Teille98/HVGene-OpenHardware/docs/Figures/Article_Figures/Fig12_XIAO_USB_Connection.jpeg

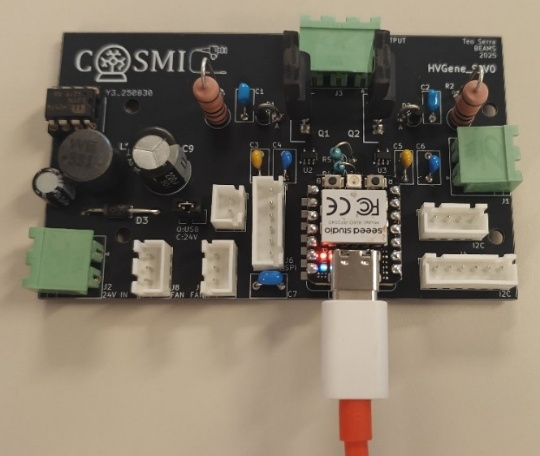
docs/Figures/Article_Figures/Fig12_XIAO_USB_Connection.jpeg
