Teille98/HVGene-OpenHardware/docs/Figures/Article_Figures/Fig_Val1_OpenCircuit.png

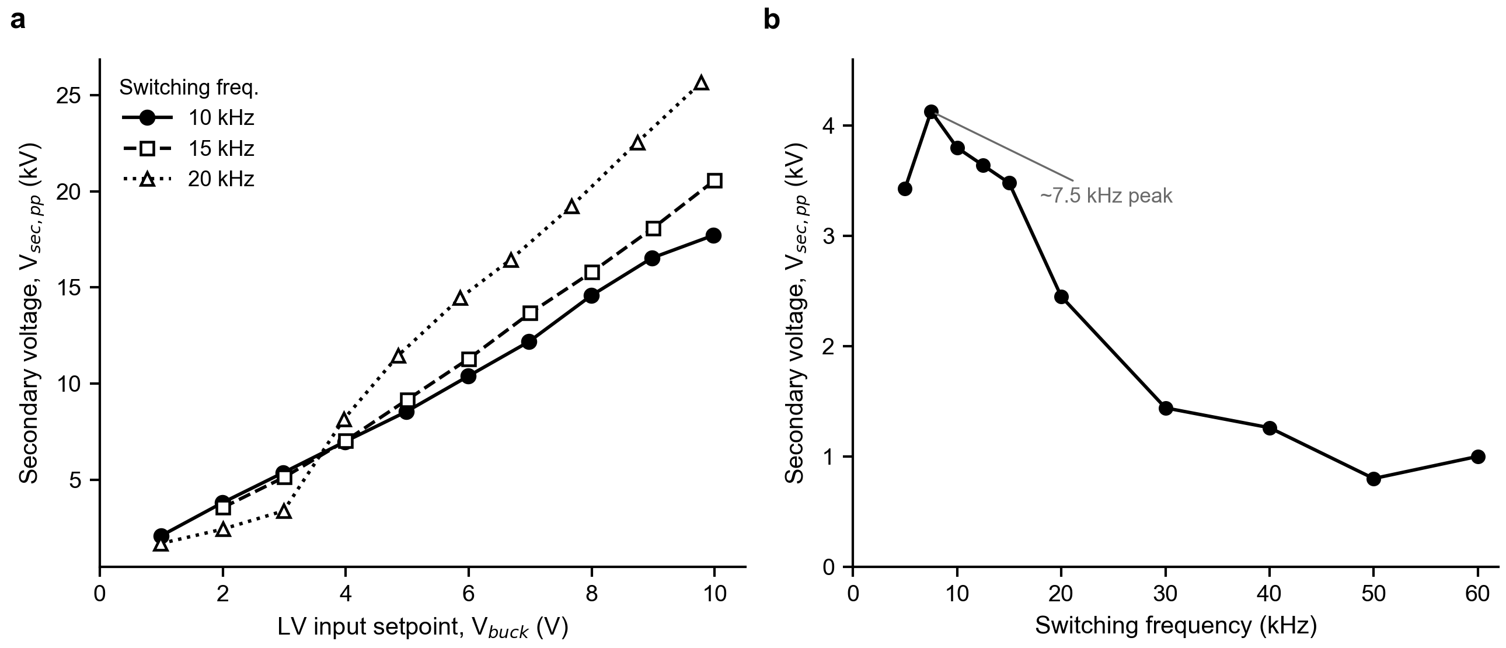
docs/Figures/Article_Figures/Fig_Val1_OpenCircuit.png
