Teille98/HVGene-OpenHardware/docs/Figures/Article_Figures/Fig_Val2_IgnitionWindow.png

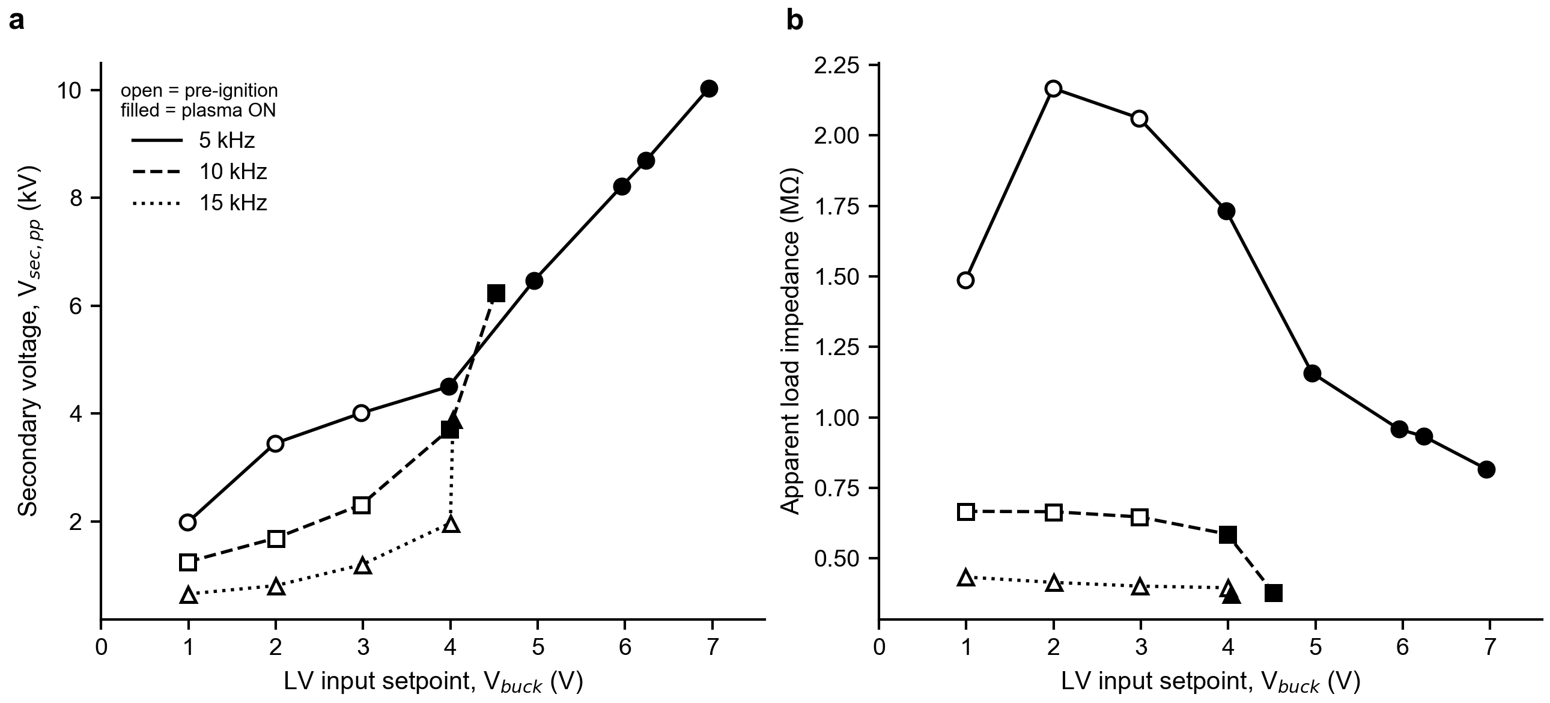
docs/Figures/Article_Figures/Fig_Val2_IgnitionWindow.png
