Teille98/HVGene-OpenHardware/docs/Figures/Article_Figures/Fig_Val3_FreqResponse.png

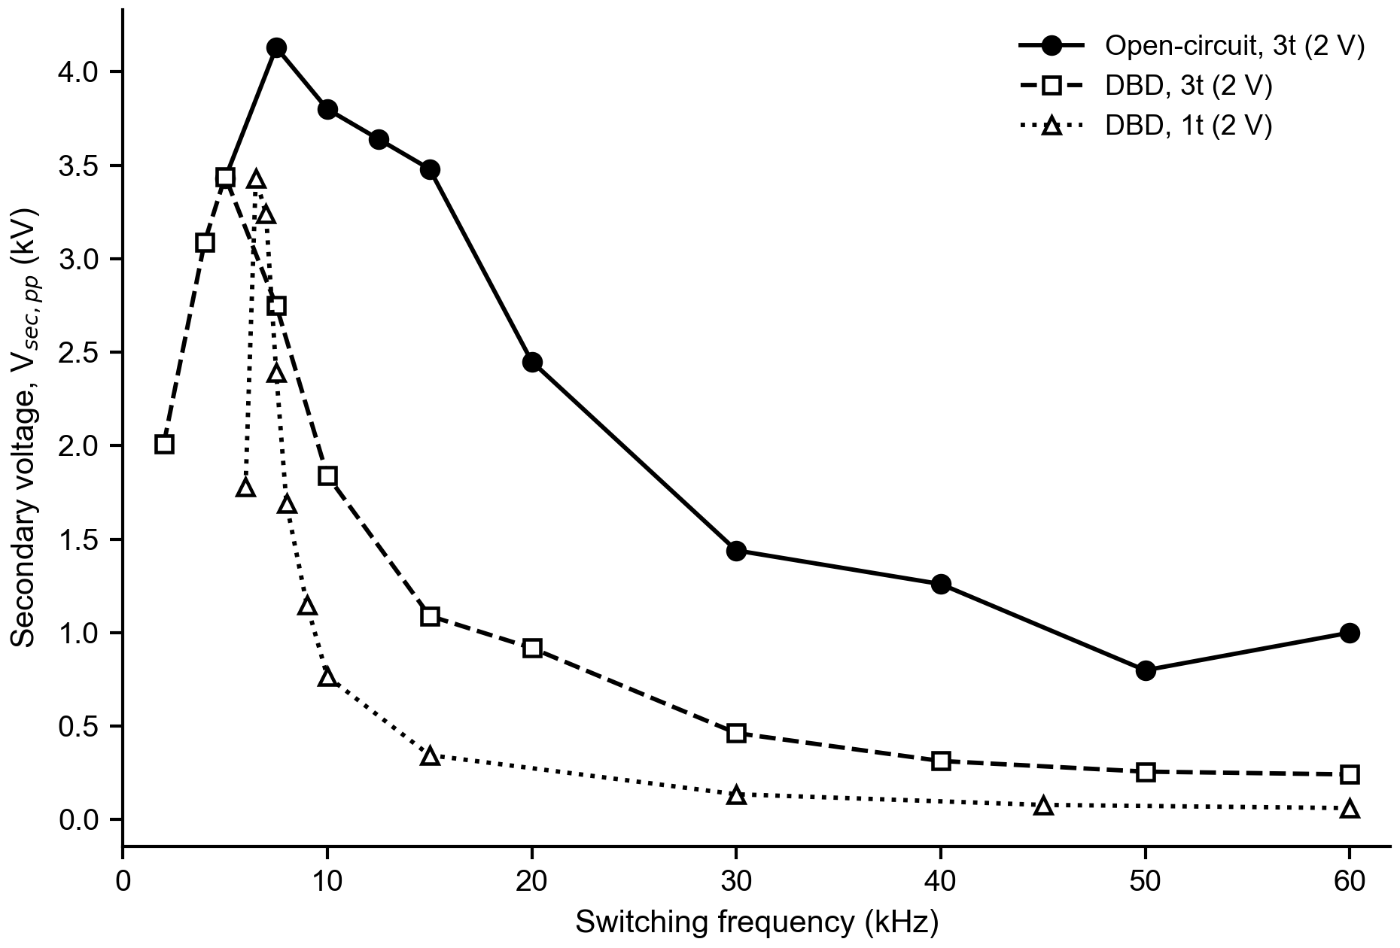
docs/Figures/Article_Figures/Fig_Val3_FreqResponse.png
