Teille98/HVGene-OpenHardware/docs/Figures/Article_Figures/Fig_Val4_DutyCycle.png

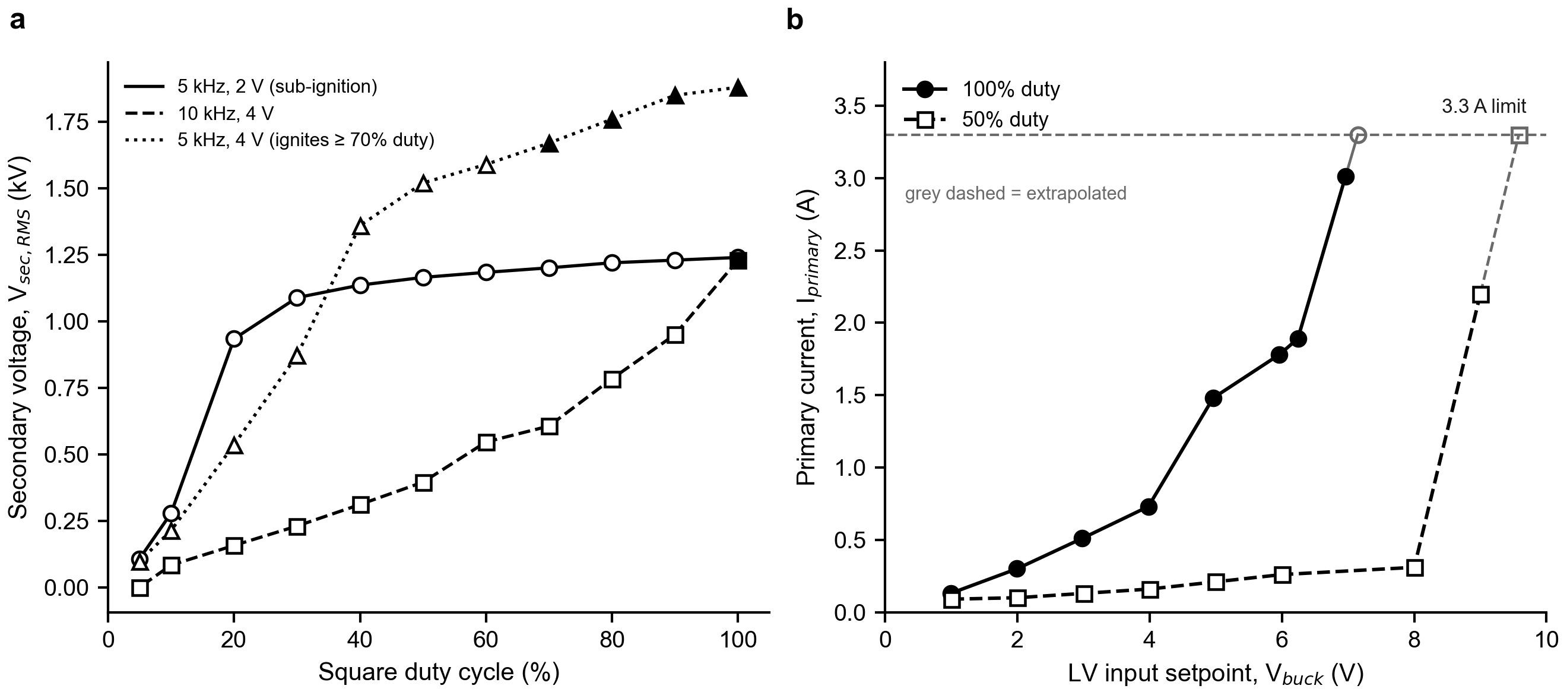
docs/Figures/Article_Figures/Fig_Val4_DutyCycle.png
