Teille98/HVGene-OpenHardware/docs/Figures/Article_Figures/Fig_Val5_Thermal.png

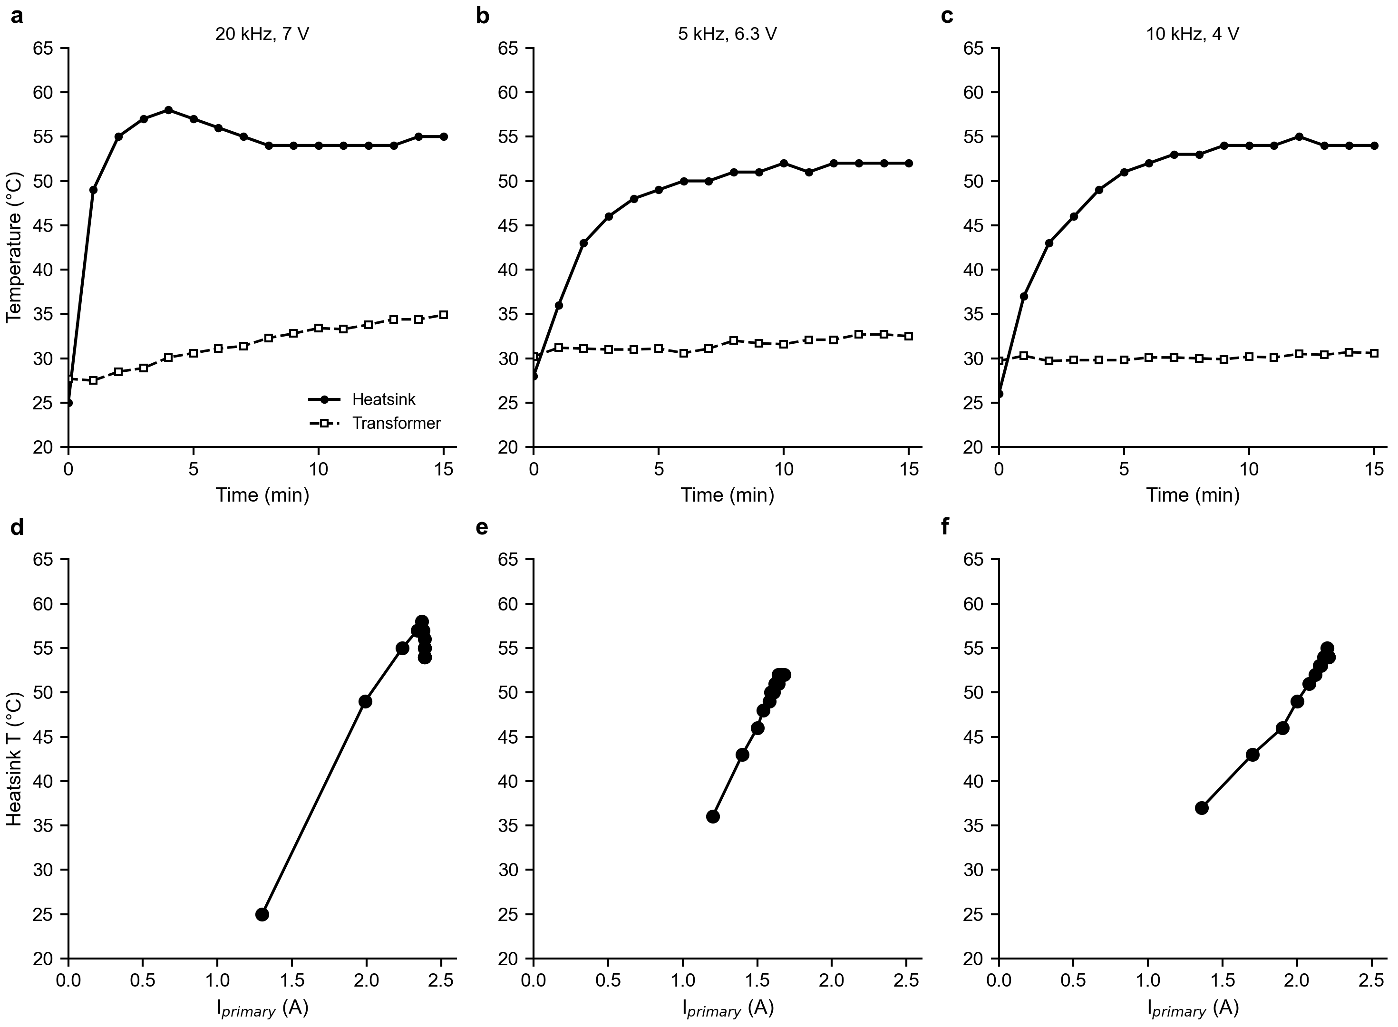
docs/Figures/Article_Figures/Fig_Val5_Thermal.png
