Teille98/HVGene-OpenHardware/docs/Figures/Article_Figures/Fig_Val6_Reproducibility.png

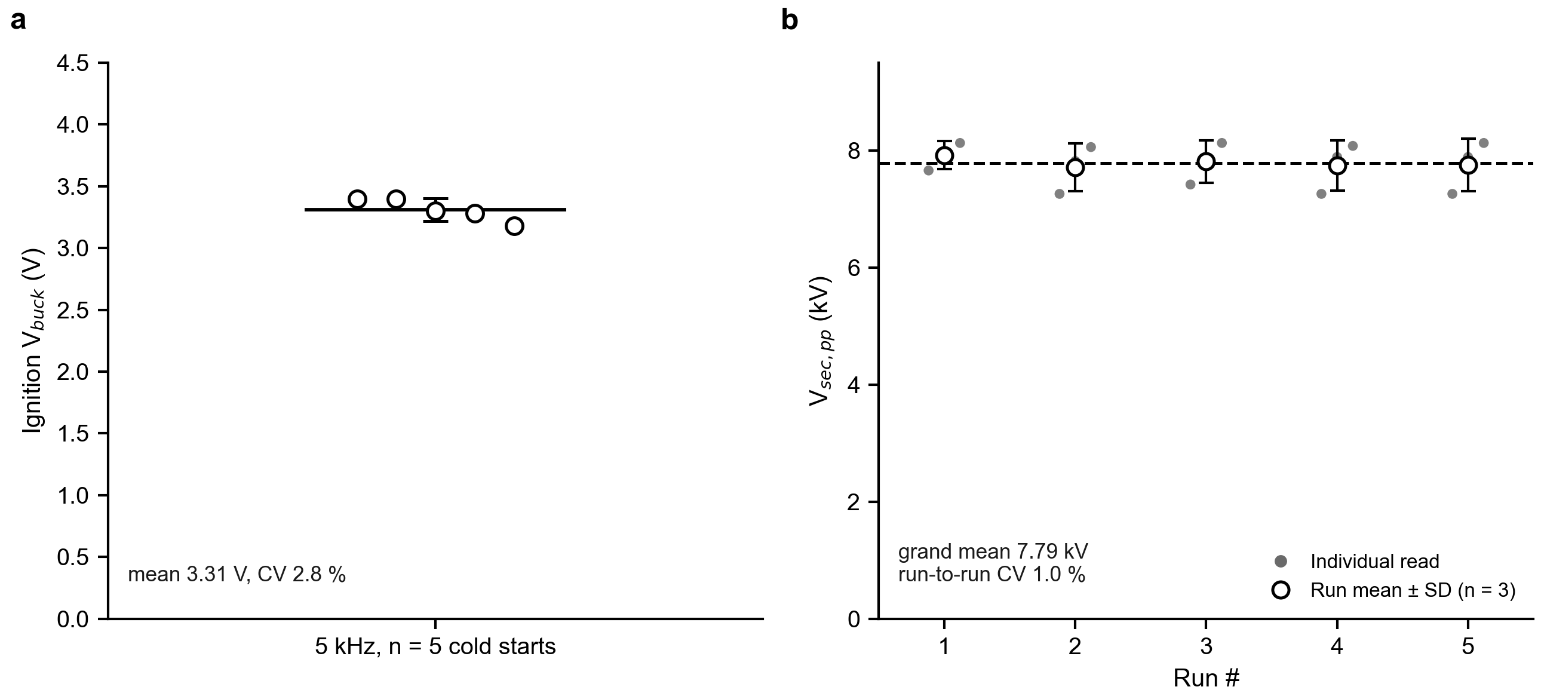
docs/Figures/Article_Figures/Fig_Val6_Reproducibility.png
