Teille98/HVGene-OpenHardware/docs/Figures/Article_Figures/Fig_Val8_THDMap.png

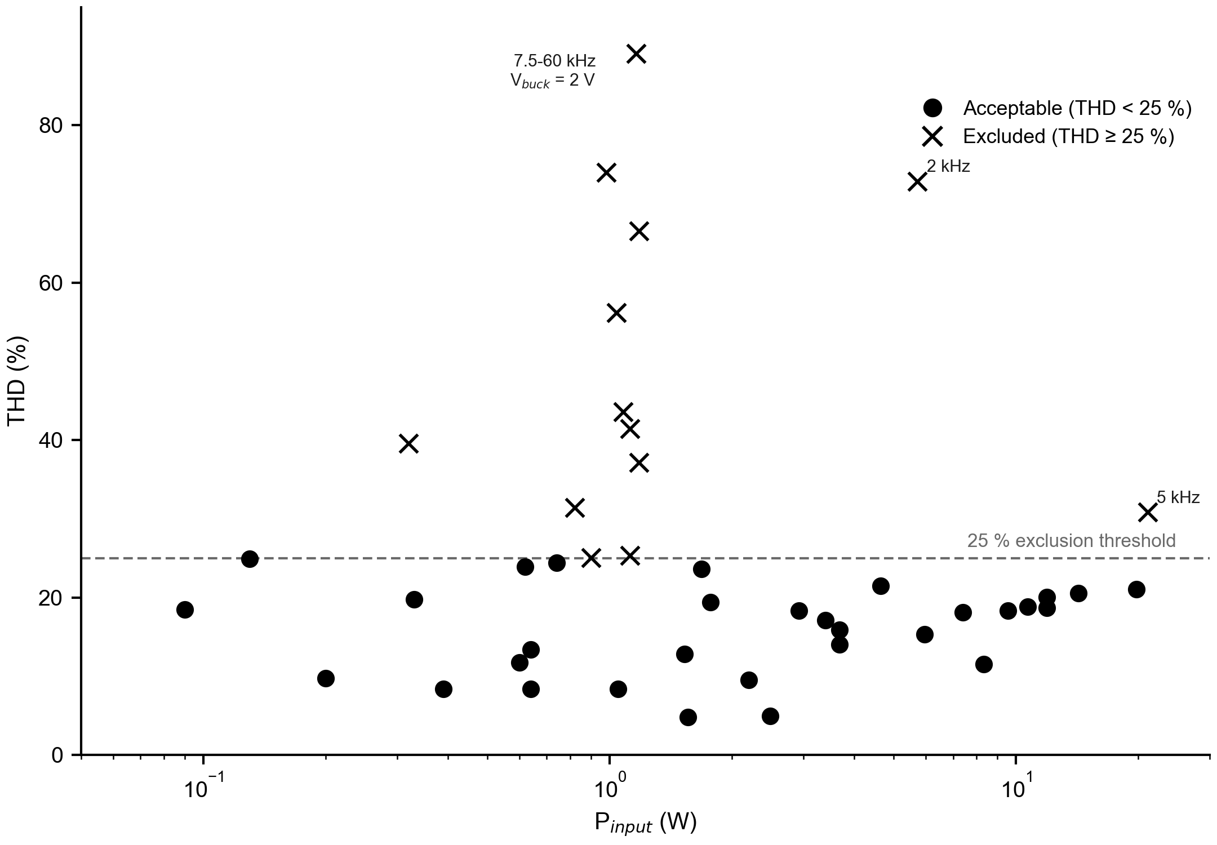
docs/Figures/Article_Figures/Fig_Val8_THDMap.png
