Teille98/HVGene-OpenHardware/docs/Figures/Article_Figures/Fig_Val9_PowerBalance.png

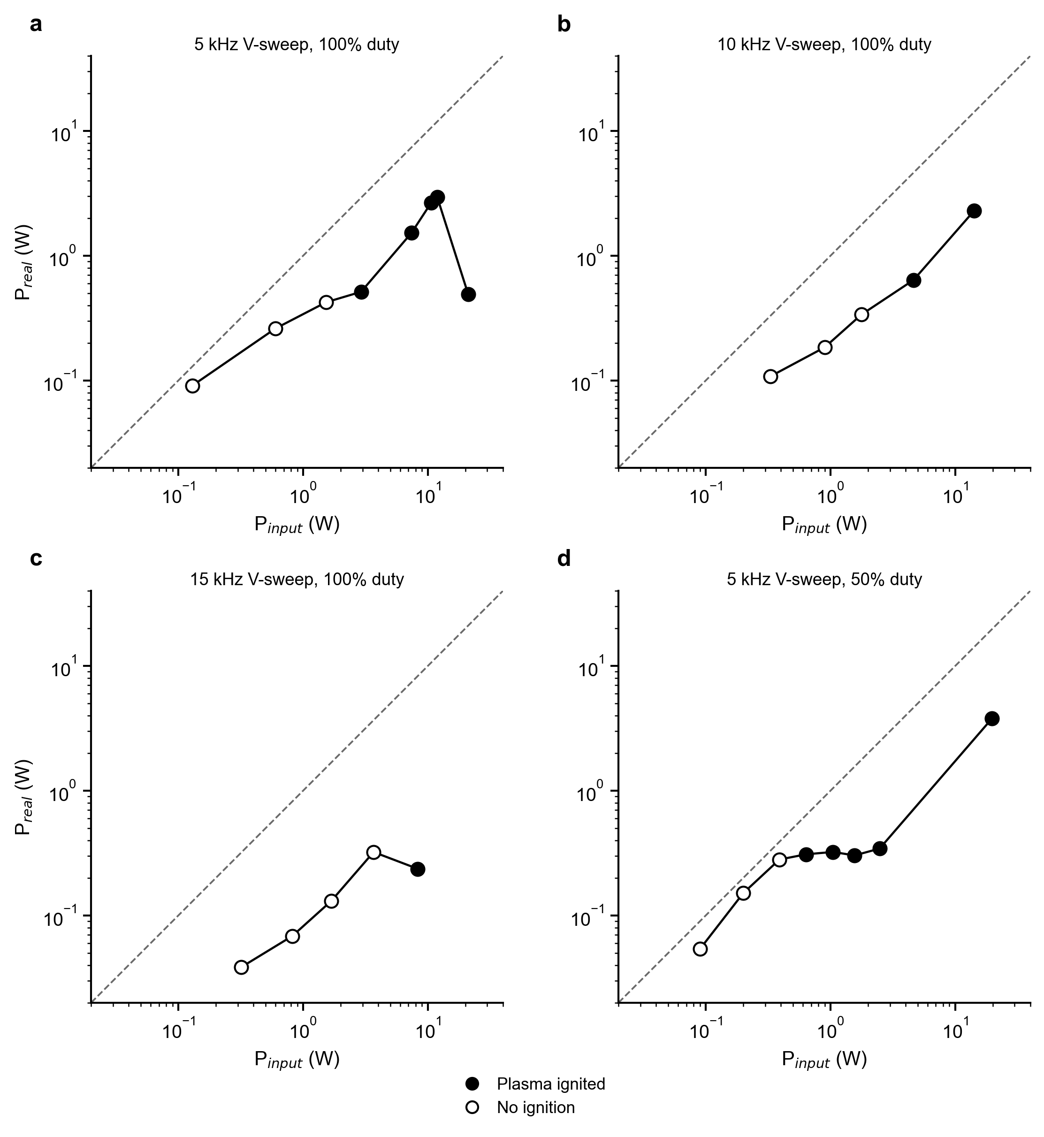
docs/Figures/Article_Figures/Fig_Val9_PowerBalance.png
