Teille98/HVGene-OpenHardware/docs/Figures/Article_Figures/Fig_Val_IgnitionPhoto.jpg

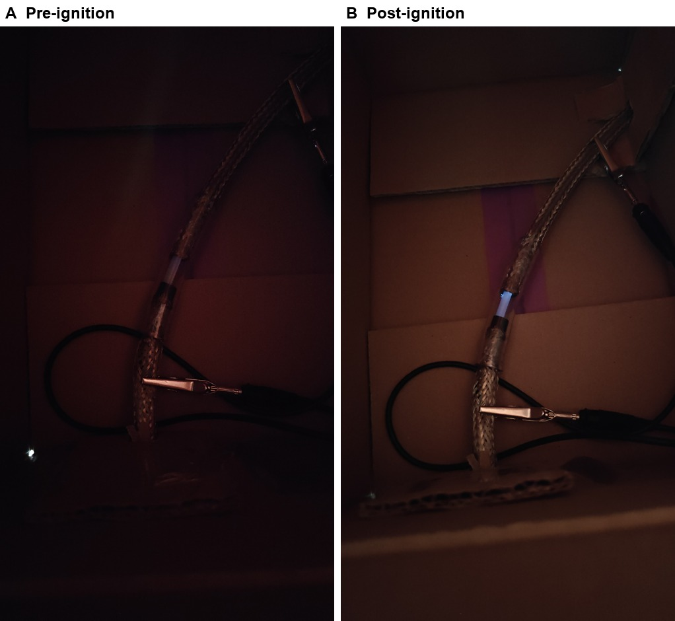
docs/Figures/Article_Figures/Fig_Val_IgnitionPhoto.jpg
