Teille98/HVGene-OpenHardware/docs/Figures/Article_Figures/Fig_Val_LmagResonance.png

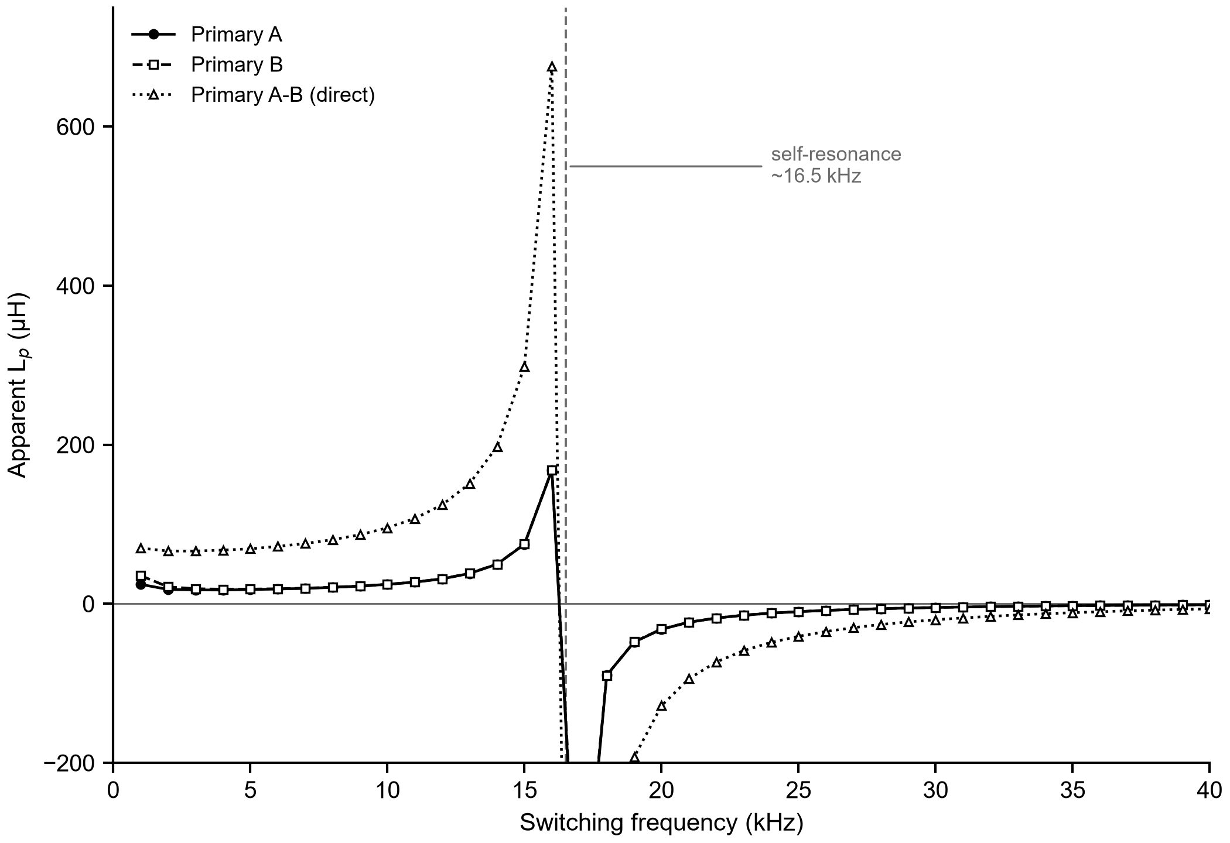
docs/Figures/Article_Figures/Fig_Val_LmagResonance.png
