Teille98/HVGene-OpenHardware/docs/Figures/Article_Figures/Fig_Val_TransfoRLC.png

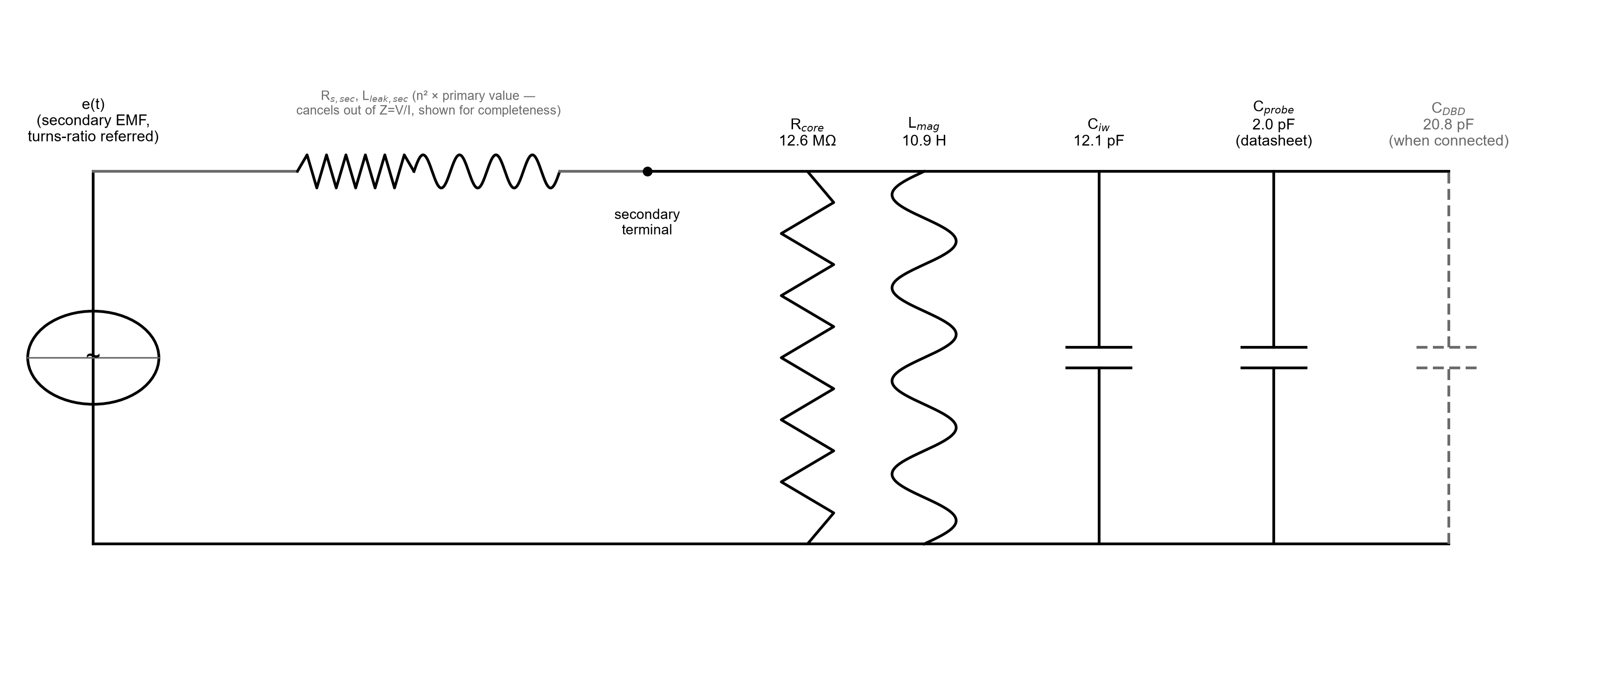
docs/Figures/Article_Figures/Fig_Val_TransfoRLC.png
