Teille98/HVGene-OpenHardware/docs/Figures/Article_Figures/Functional_Block_Diagram_v1.png

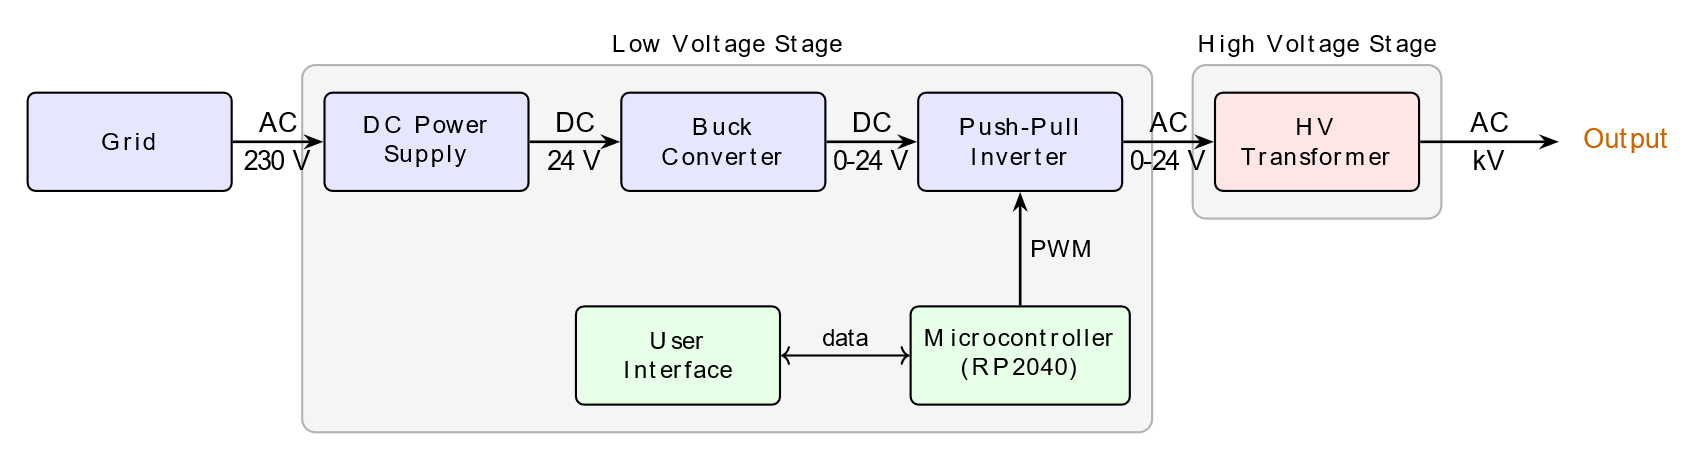
docs/Figures/Article_Figures/Functional_Block_Diagram_v1.png
