Teille98/HVGene-OpenHardware/docs/Figures/Article_Figures/KiCad_Schematic_v1.png

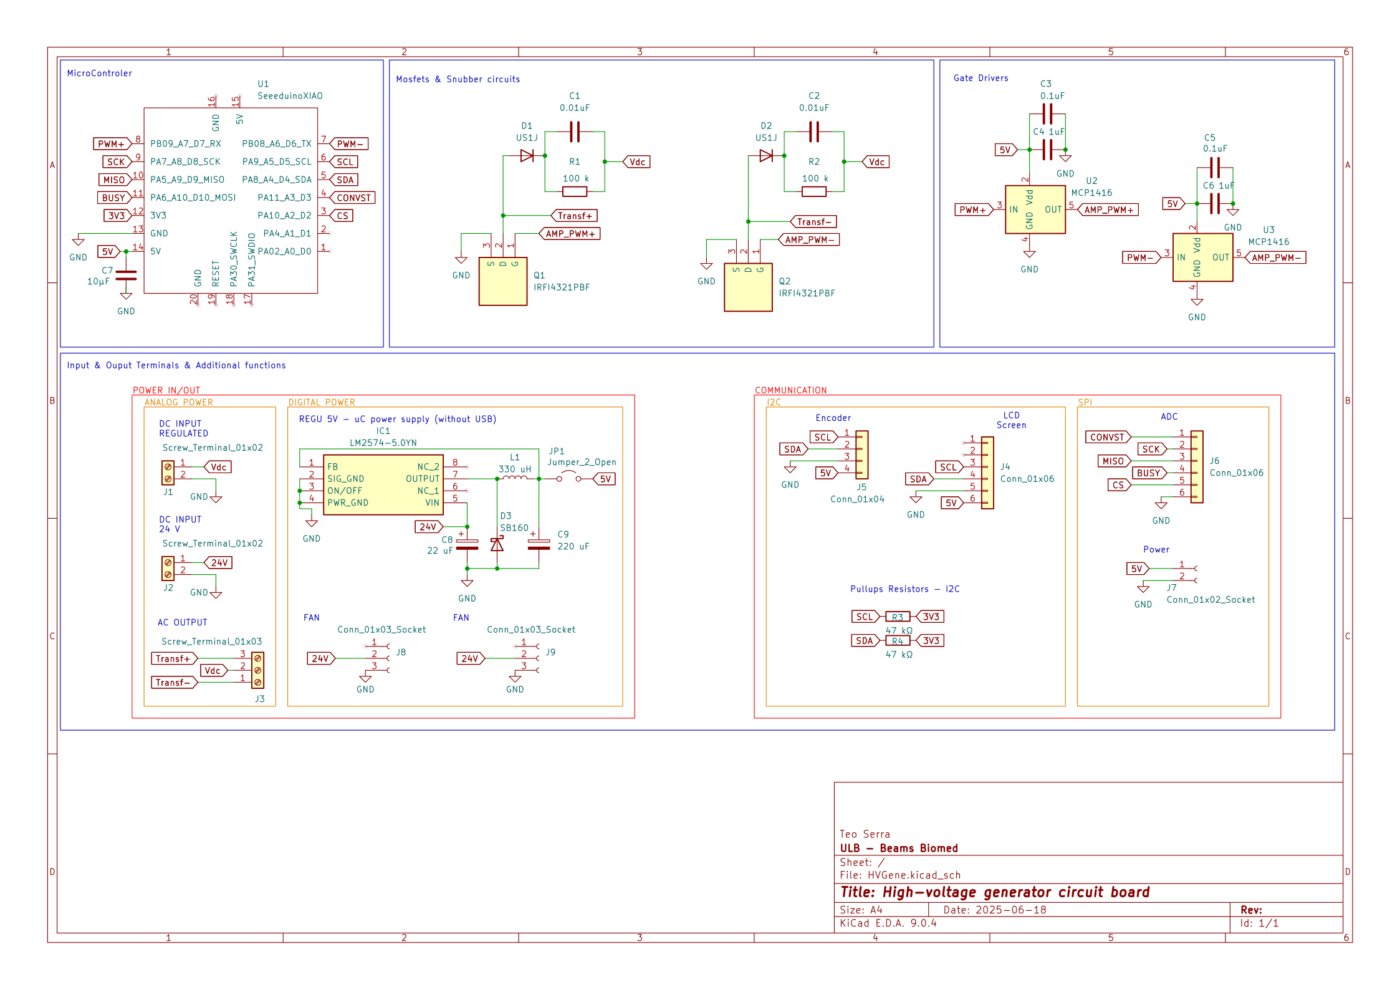
docs/Figures/Article_Figures/KiCad_Schematic_v1.png
