Teille98/HVGene-OpenHardware/docs/Figures/Article_Figures/PCB_3D_Render_v1.png

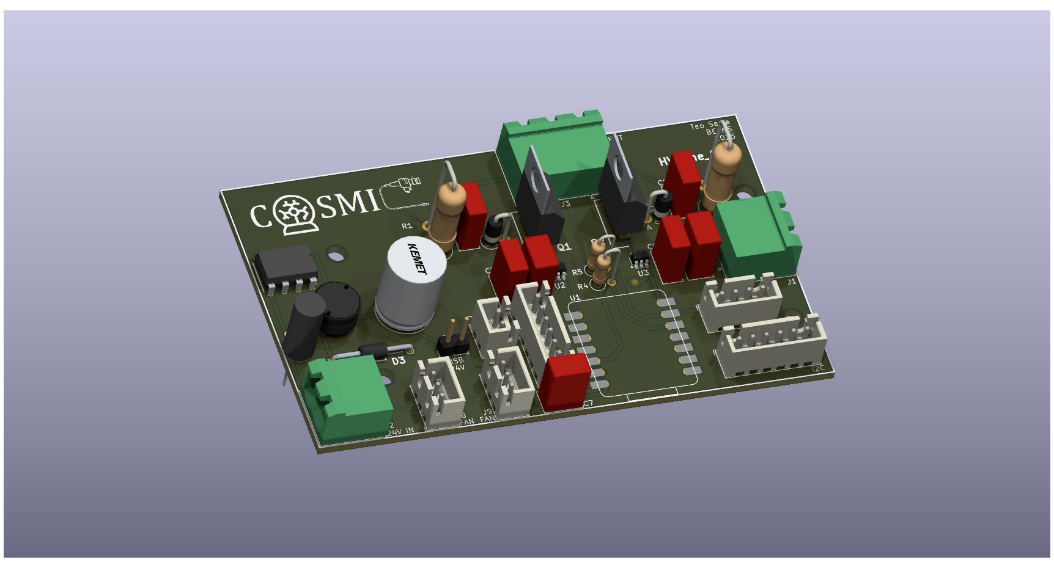
docs/Figures/Article_Figures/PCB_3D_Render_v1.png
