Teille98/HVGene-OpenHardware/docs/Figures/Article_Figures/PCB_Layout_Render.png

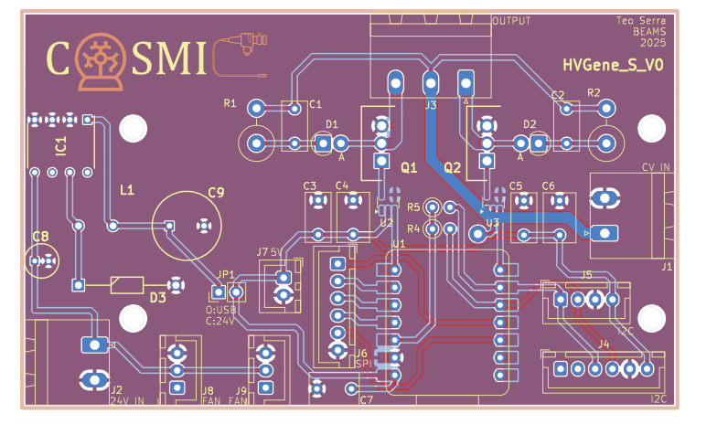
docs/Figures/Article_Figures/PCB_Layout_Render.png
