Teille98/HVGene-OpenHardware/docs/Figures/Article_Figures/PushPull_Principle_Diagram.png

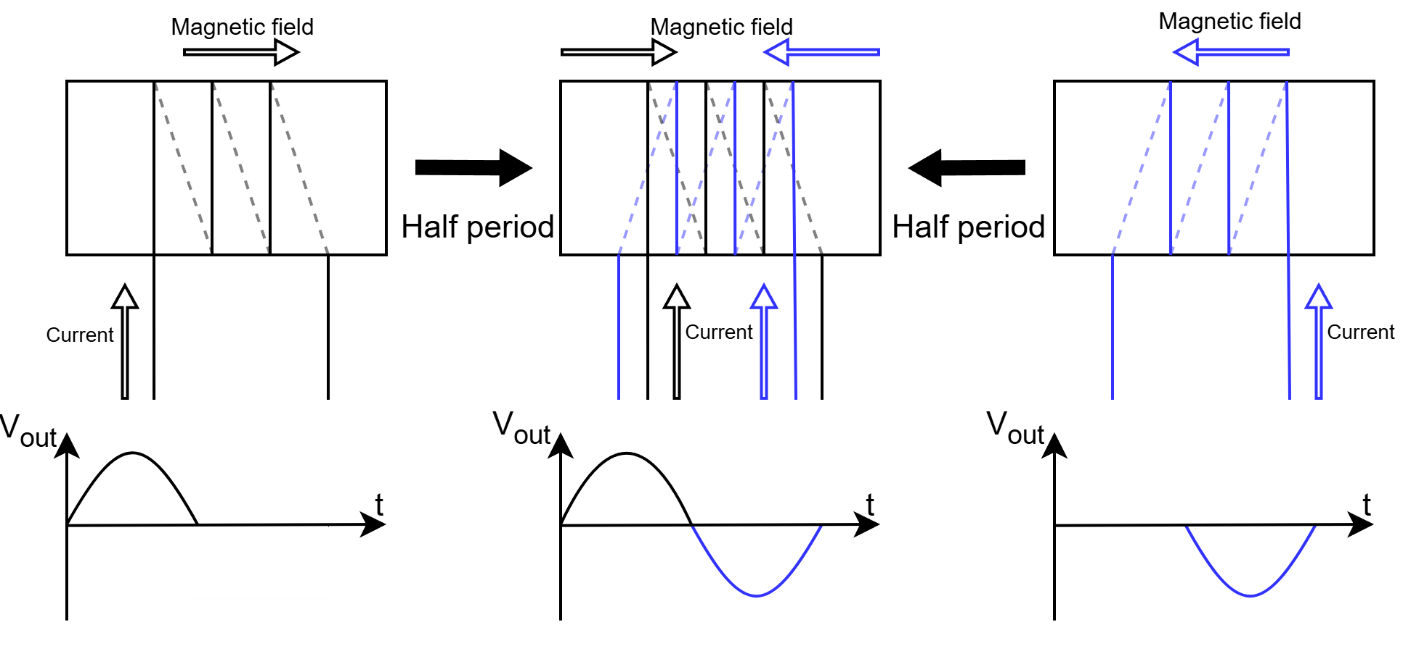
docs/Figures/Article_Figures/PushPull_Principle_Diagram.png
