Teille98/HVGene-OpenHardware/docs/Figures/Article_Figures/Transformer_Winding_Principle_Diagram.png

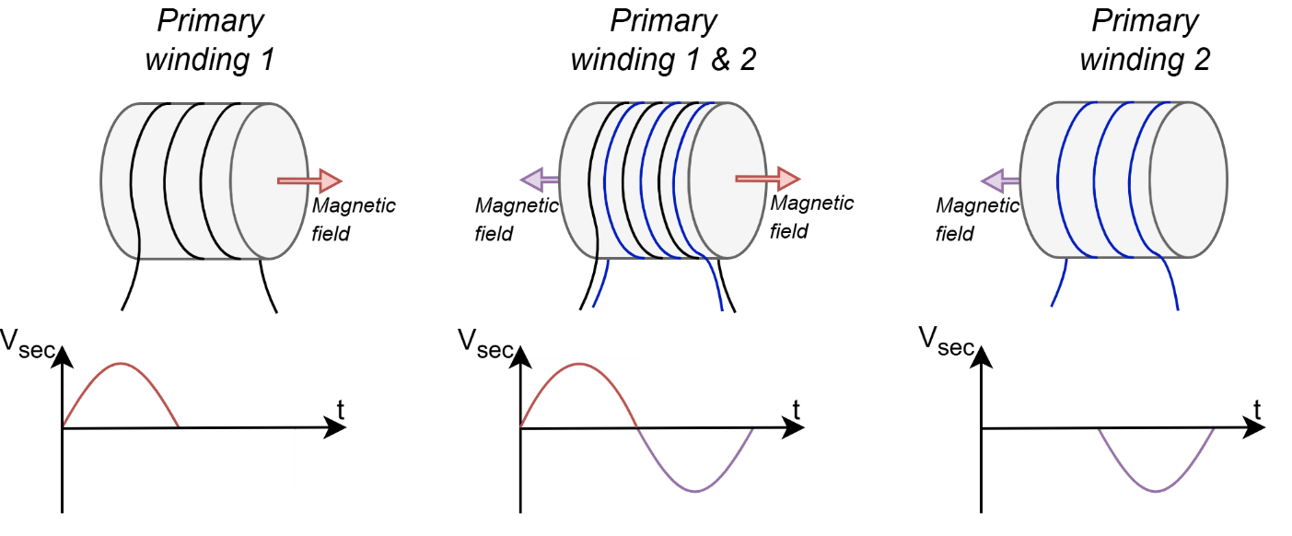
docs/Figures/Article_Figures/Transformer_Winding_Principle_Diagram.png
