Teille98/HVGene-OpenHardware/docs/Figures/CAD_Renders/HV_comp_plate_hv_bottom.png

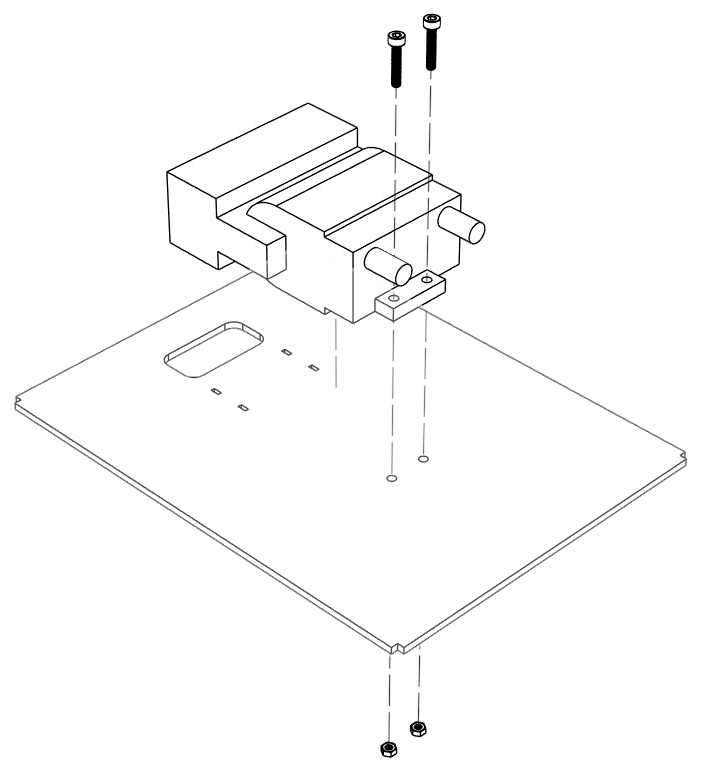
docs/Figures/CAD_Renders/HV_comp_plate_hv_bottom.png
