Teille98/HVGene-OpenHardware/docs/Figures/CAD_Renders/HV_comp_plate_hv_front.png

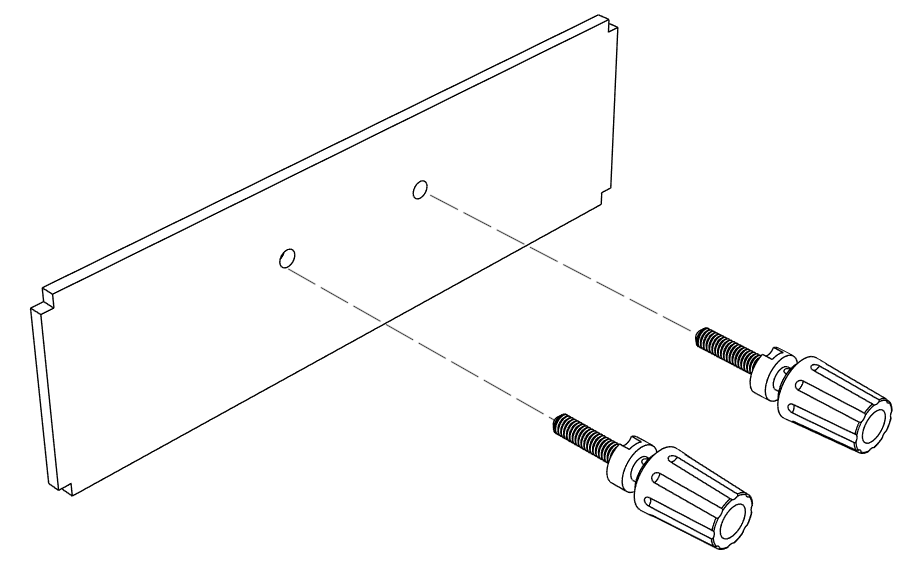
docs/Figures/CAD_Renders/HV_comp_plate_hv_front.png
