Teille98/HVGene-OpenHardware/docs/Figures/CAD_Renders/LV_SIDE_COMP_2.png

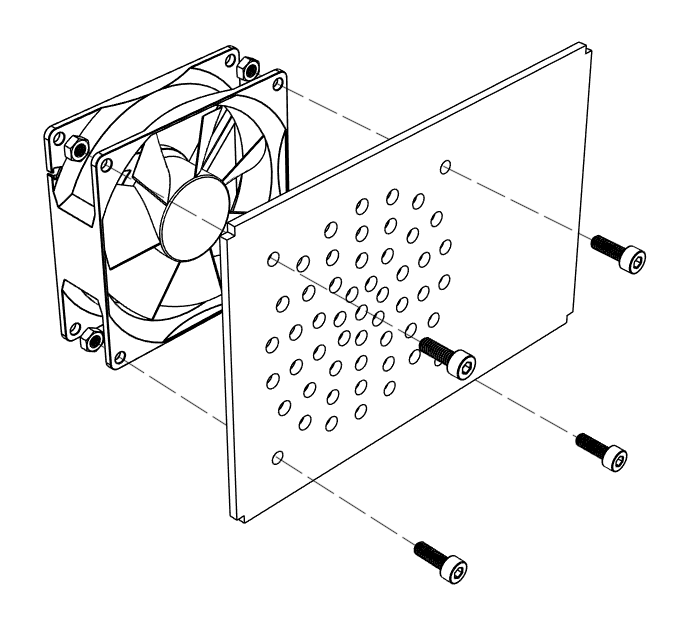
docs/Figures/CAD_Renders/LV_SIDE_COMP_2.png
