Teille98/HVGene-OpenHardware/docs/Figures/CAD_Renders/LV_TOP_COMP.png

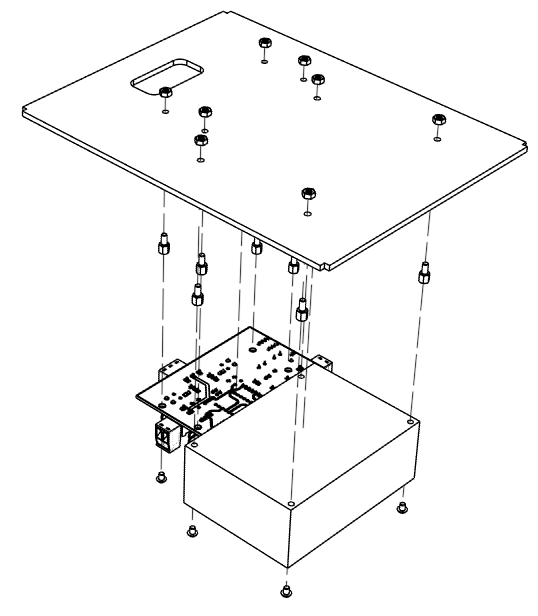
docs/Figures/CAD_Renders/LV_TOP_COMP.png
