Teille98/HVGene-OpenHardware/docs/Figures/Device_Photos/IMG20260715170636.jpg

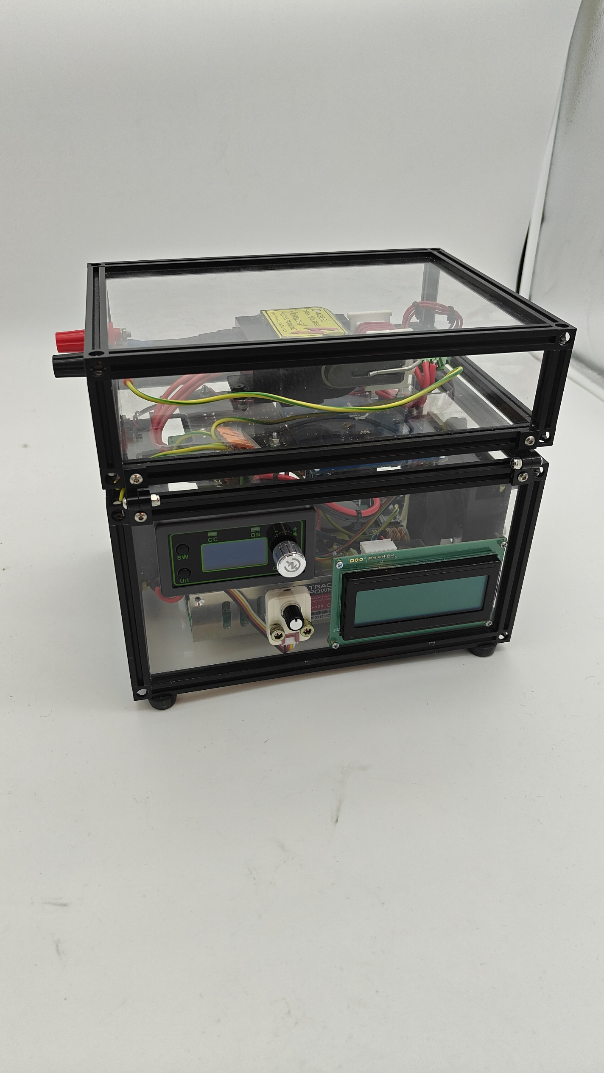
docs/Figures/Device_Photos/IMG20260715170636.jpg
