Teille98/HVGene-OpenHardware/docs/Figures/Device_Photos/IMG20260715170657.jpg

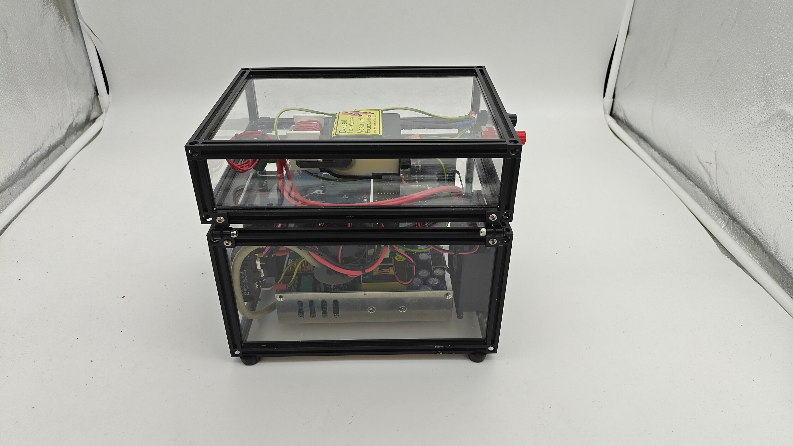
docs/Figures/Device_Photos/IMG20260715170657.jpg
