Teille98/HVGene-OpenHardware/docs/Figures/Device_Photos/IMG20260715170715-R.jpg

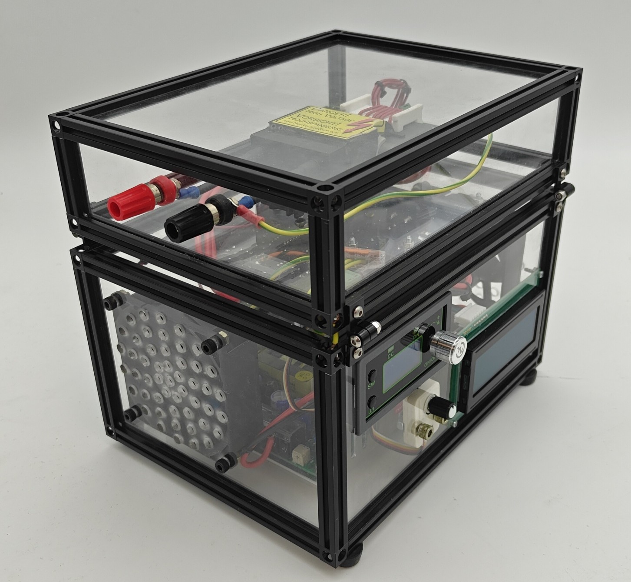
docs/Figures/Device_Photos/IMG20260715170715-R.jpg
