Teille98/HVGene-OpenHardware/docs/Figures/Device_Photos/IMG20260715170749.jpg

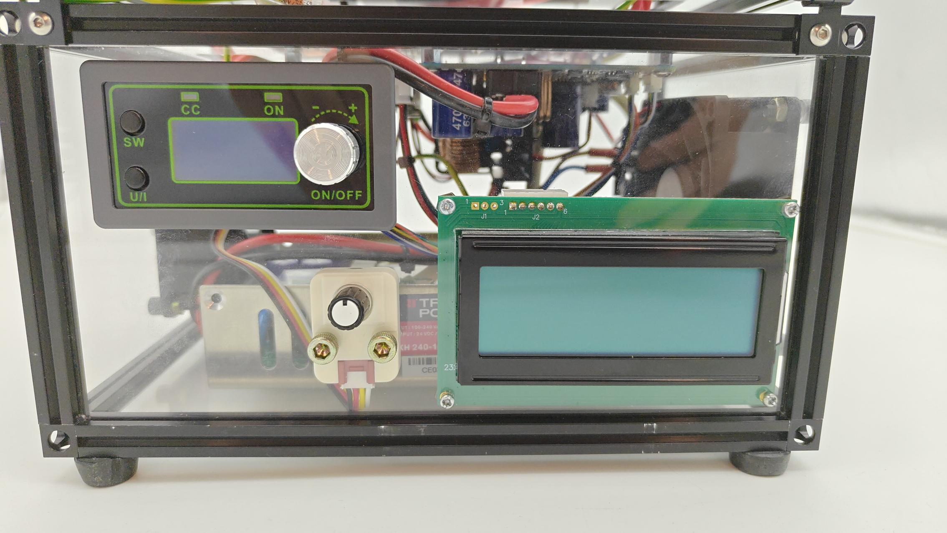
docs/Figures/Device_Photos/IMG20260715170749.jpg
