Teille98/HVGene-OpenHardware/docs/Figures/Diagrams/cross-section_DBD-Figure V2.drawio.png

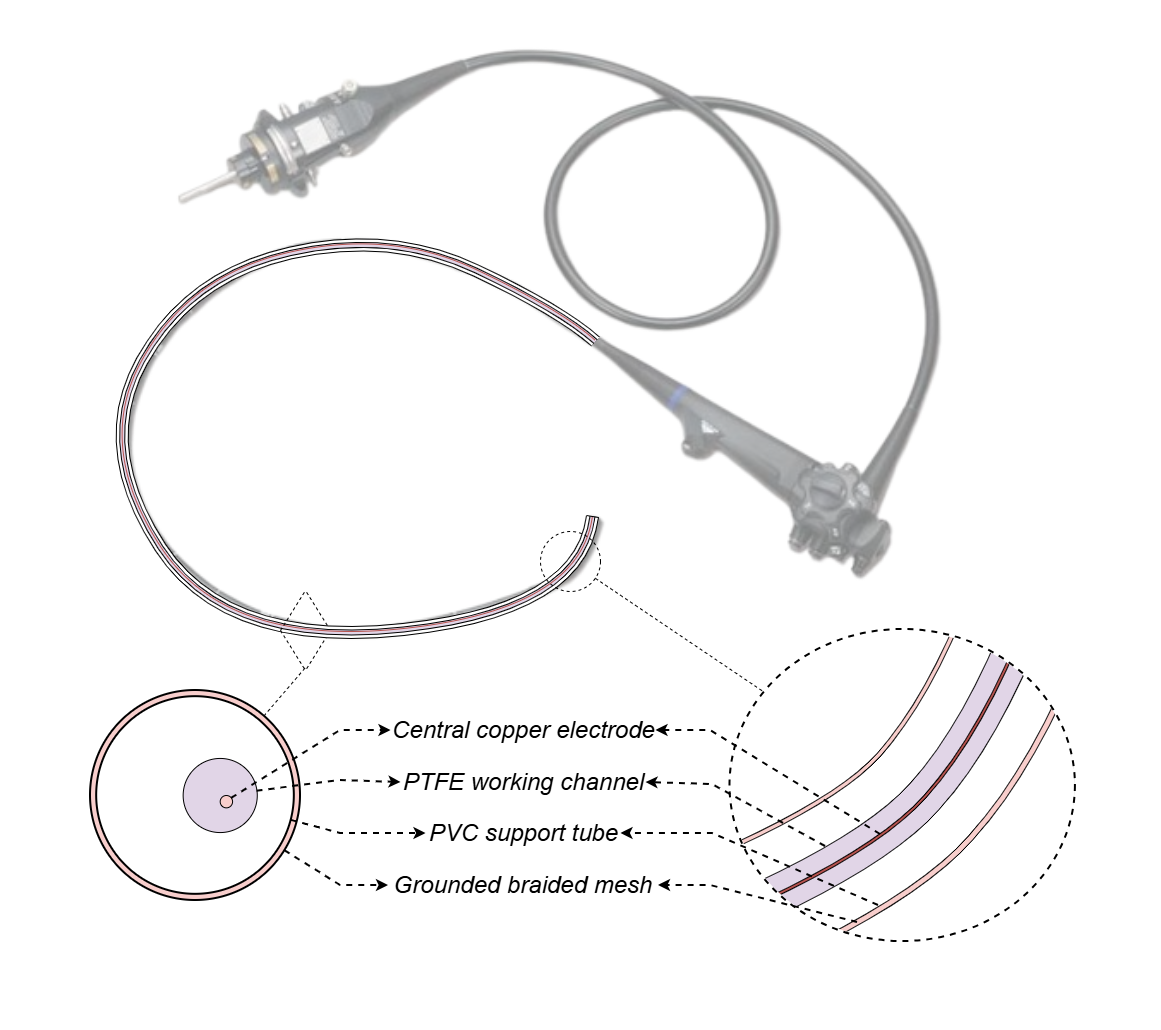
docs/Figures/Diagrams/cross-section_DBD-Figure V2.drawio.png
