Teille98/HVGene-OpenHardware/docs/Figures/Diagrams/gaz_diagram-V2.drawio.png

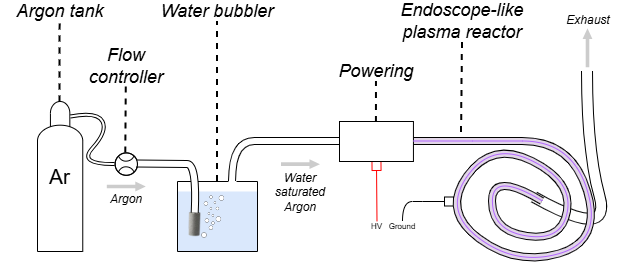
docs/Figures/Diagrams/gaz_diagram-V2.drawio.png
