Teille98/HVGene-OpenHardware/docs/Figures/Diagrams/HVGene_elec_diagram.drawio.png

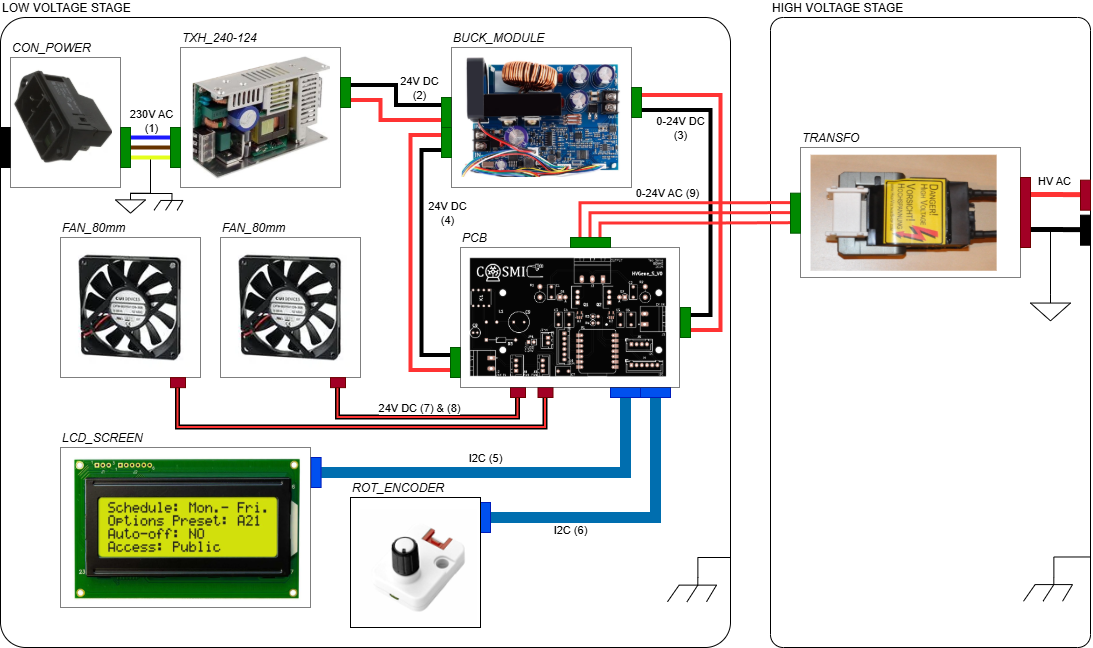
docs/Figures/Diagrams/HVGene_elec_diagram.drawio.png
