Teille98/HVGene-OpenHardware/docs/Figures/Diagrams/HVGene_elec_diagram_opa.drawio.png

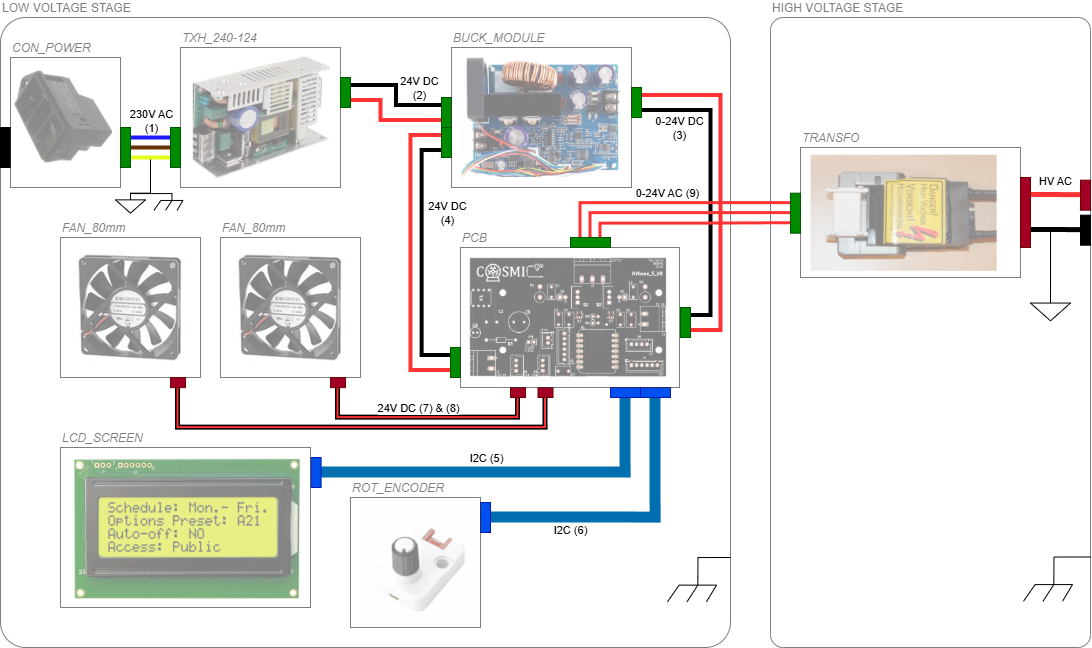
docs/Figures/Diagrams/HVGene_elec_diagram_opa.drawio.png
