Teille98/HVGene-OpenHardware/docs/Figures/Diagrams/HVGene_elec_diagram_V2.drawio.png

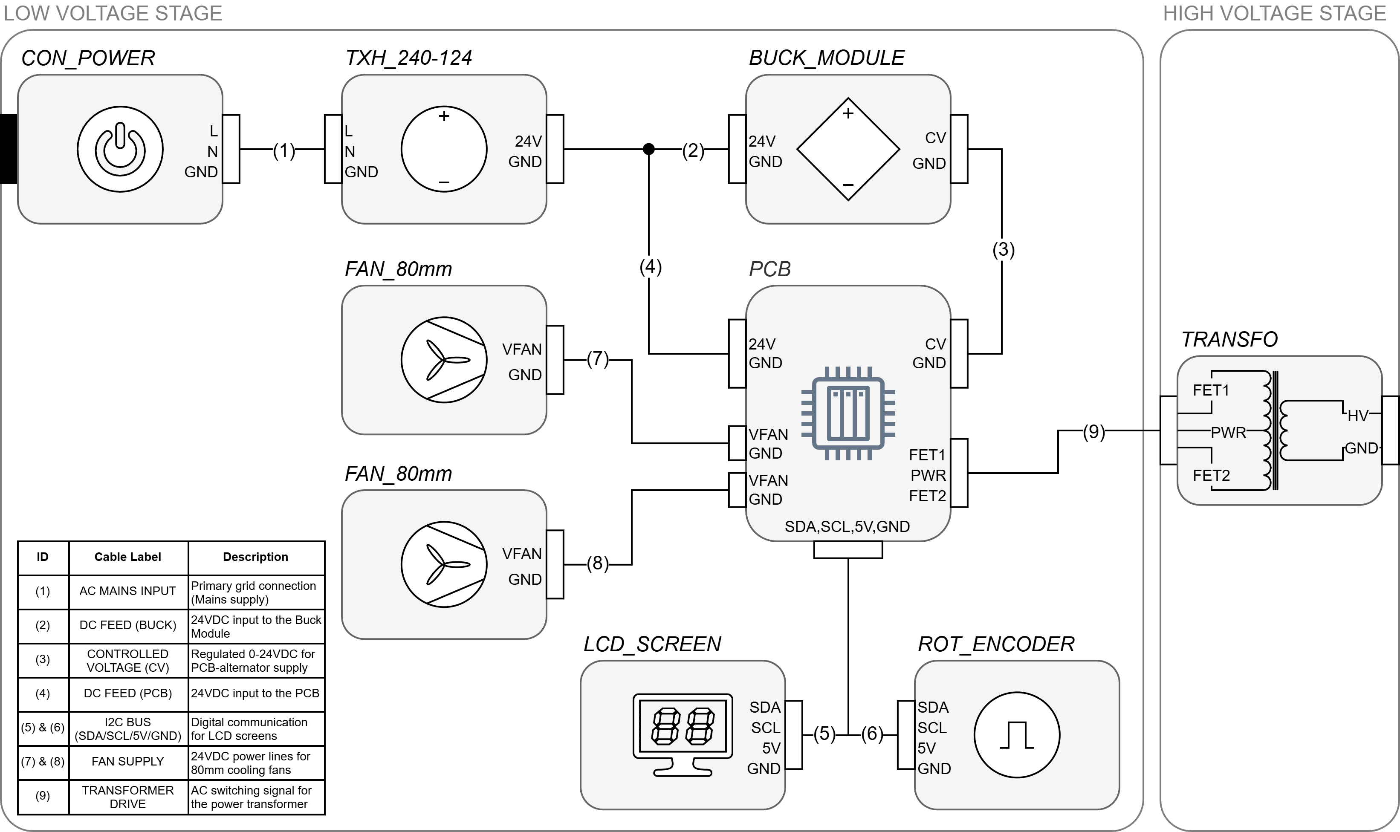
docs/Figures/Diagrams/HVGene_elec_diagram_V2.drawio.png
