Teille98/HVGene-OpenHardware/docs/Figures/Diagrams/Impression_Schématique.png

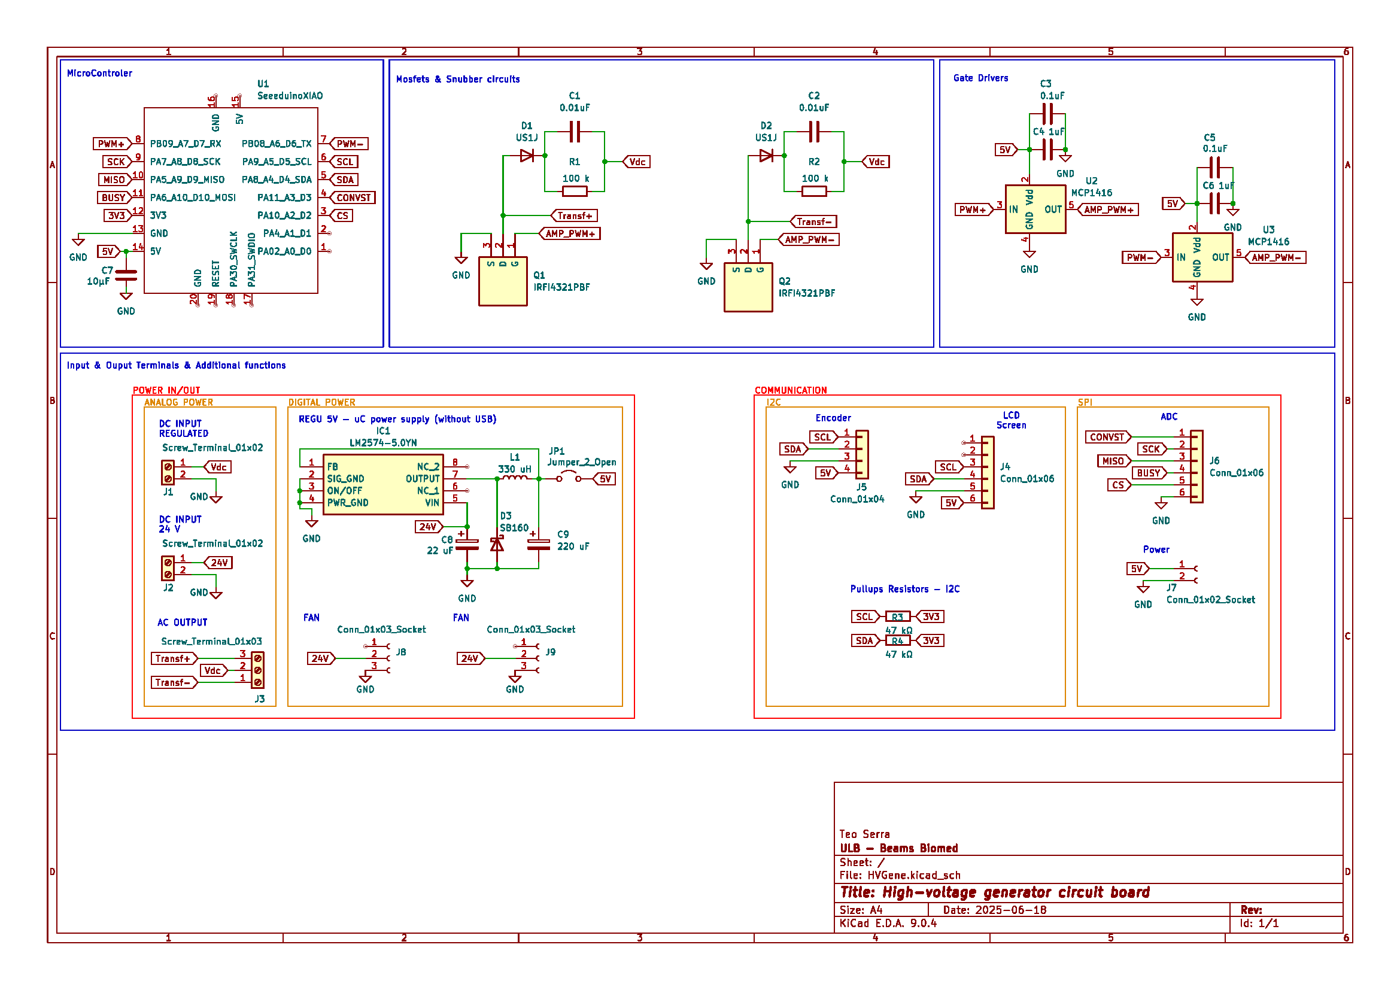
docs/Figures/Diagrams/Impression_Schématique.png
