Teille98/HVGene-OpenHardware/docs/Figures/Plasma_Photos/plasma_off.jpg

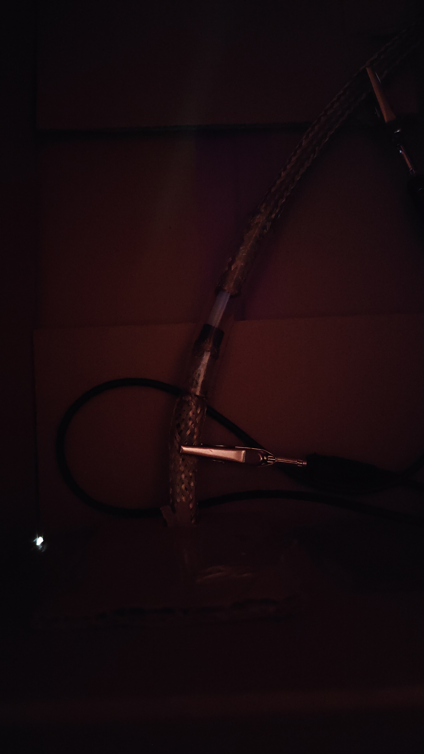
docs/Figures/Plasma_Photos/plasma_off.jpg
