Teille98/HVGene-OpenHardware/docs/Figures/Plasma_Photos/plasma_off_2.jpg

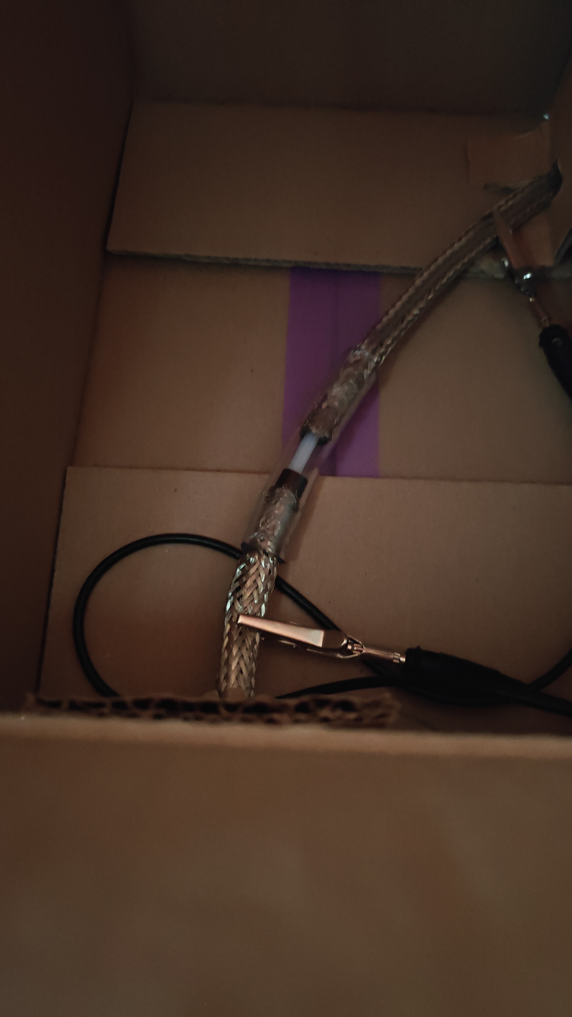
docs/Figures/Plasma_Photos/plasma_off_2.jpg
