Teille98/HVGene-OpenHardware/docs/Figures/Plasma_Photos/plasma_on.jpg

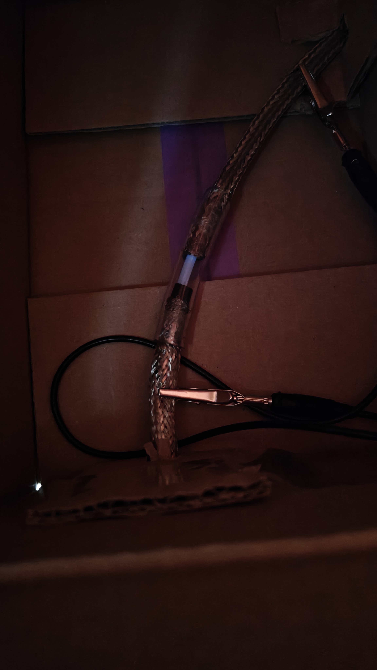
docs/Figures/Plasma_Photos/plasma_on.jpg
