Teille98/HVGene-OpenHardware/docs/Figures/Plasma_Photos/plasma_on_4.jpg

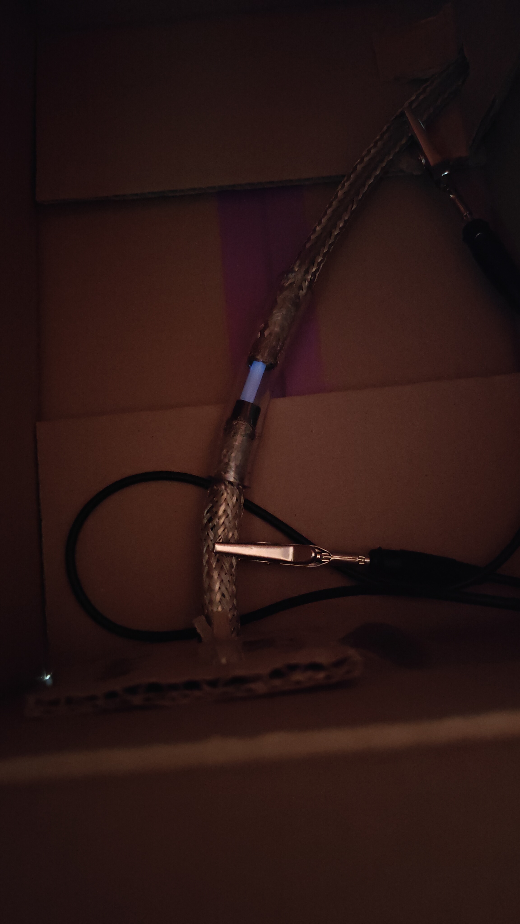
docs/Figures/Plasma_Photos/plasma_on_4.jpg
