Teille98/HVGene-OpenHardware/docs/Figures/Plasma_Photos/plasma_on_filament.jpg

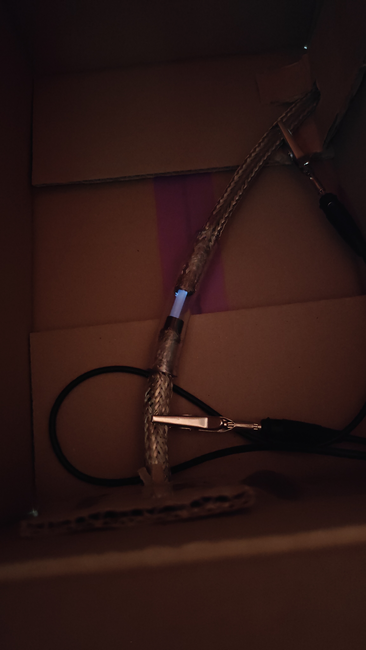
docs/Figures/Plasma_Photos/plasma_on_filament.jpg
