Teille98/HVGene-OpenHardware/docs/Figures/Plasma_Photos/plasma_on_filament_3.jpg

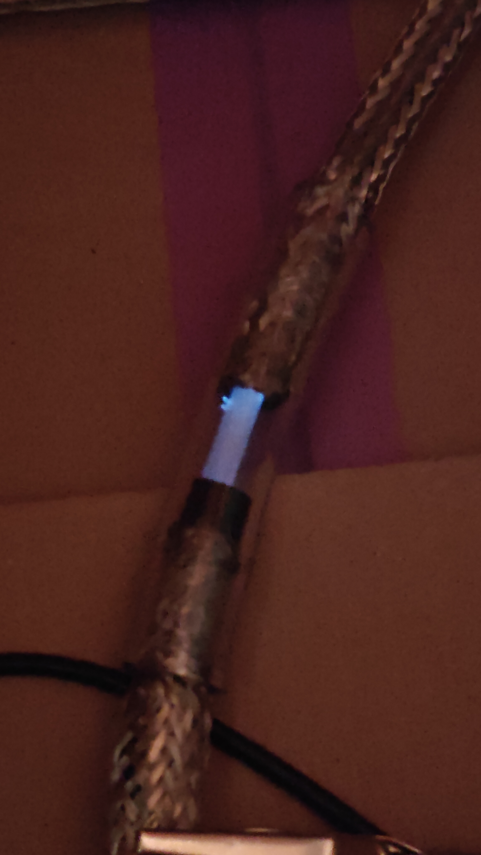
docs/Figures/Plasma_Photos/plasma_on_filament_3.jpg
