Teille98/HVGene-OpenHardware/docs/Figures/Scope_Captures/Exp1_PIC_1818_2_16052026.png

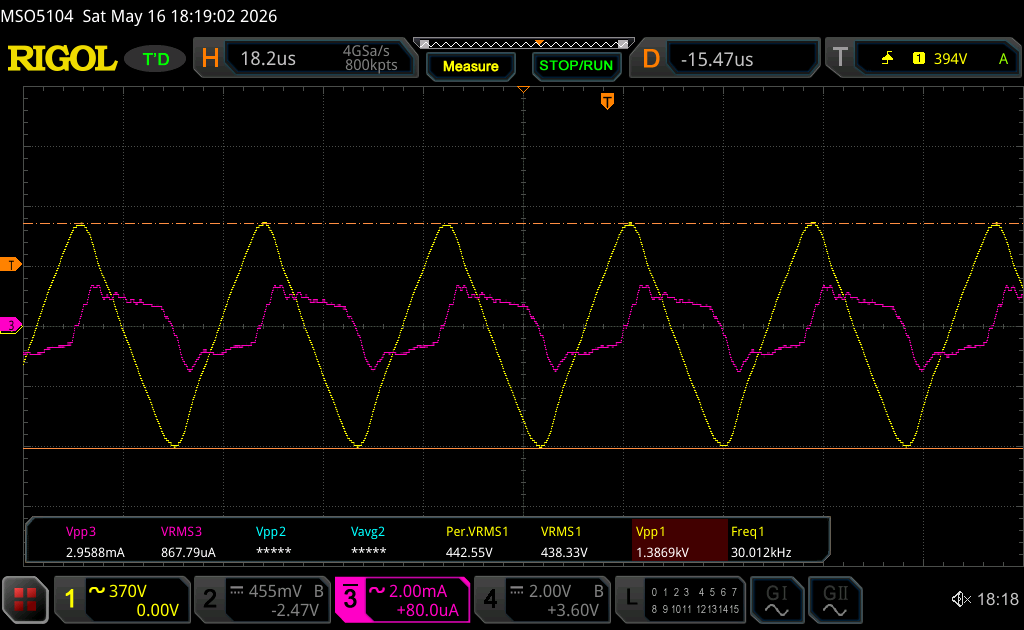
docs/Figures/Scope_Captures/Exp1_PIC_1818_2_16052026.png
