Teille98/HVGene-OpenHardware/docs/Figures/Scope_Captures/Exp2_1_PIC_1924_19052026.png

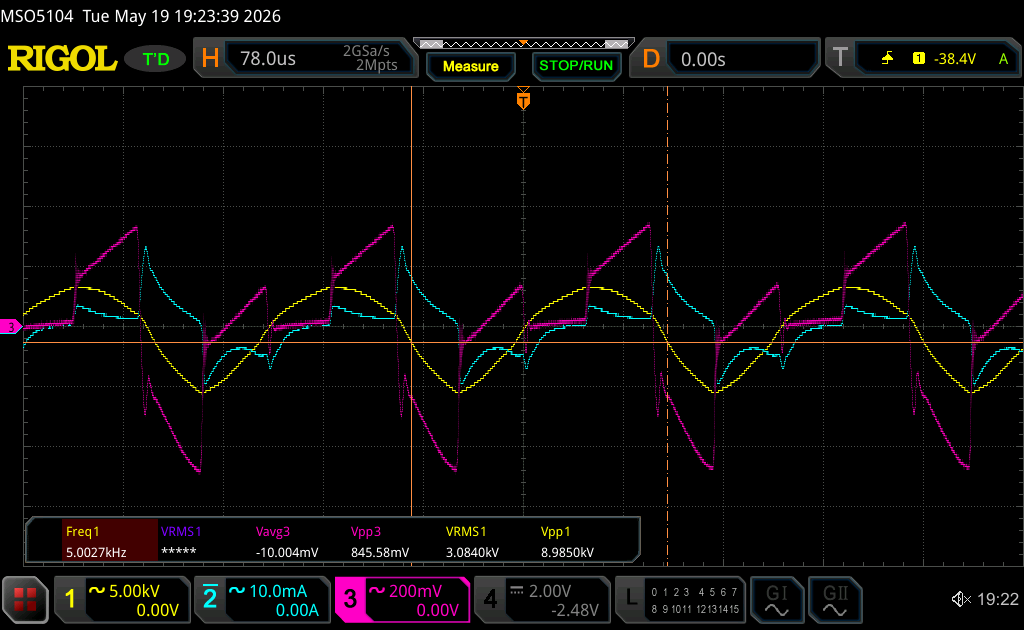
docs/Figures/Scope_Captures/Exp2_1_PIC_1924_19052026.png
