Teille98/HVGene-OpenHardware/docs/Figures/Scope_Captures/Exp2_3_PIC_1725_19052026.png

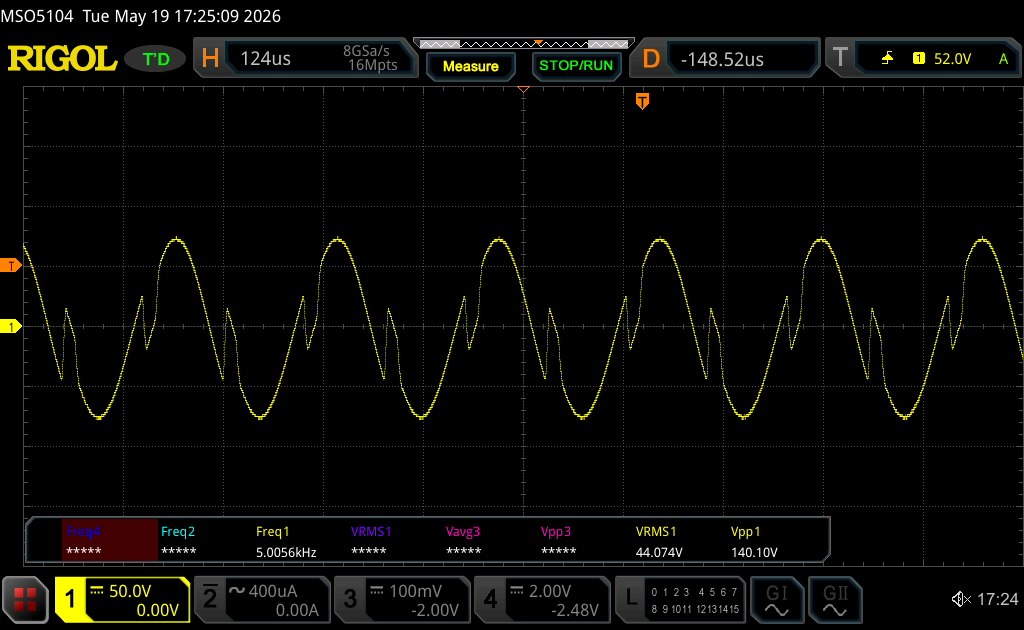
docs/Figures/Scope_Captures/Exp2_3_PIC_1725_19052026.png
