Teille98/HVGene-OpenHardware/docs/Figures/Scope_Captures/not_defined_PIC_1734_15052026.png

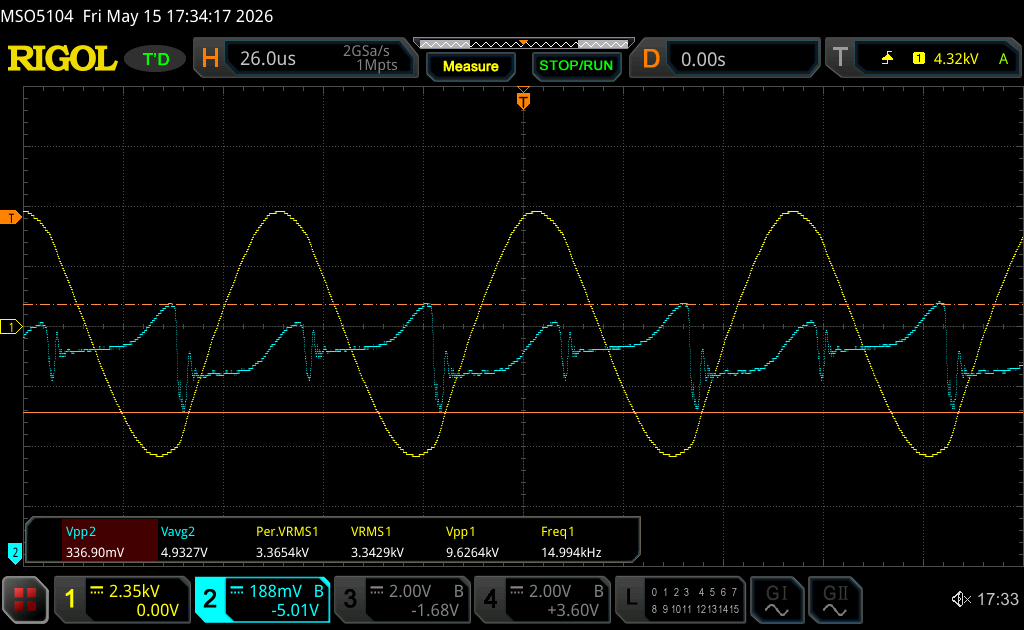
docs/Figures/Scope_Captures/not_defined_PIC_1734_15052026.png
