Teille98/HVGene-OpenHardware/docs/Figures/Scope_Captures/not_defined_PIC_2116_16052026.png

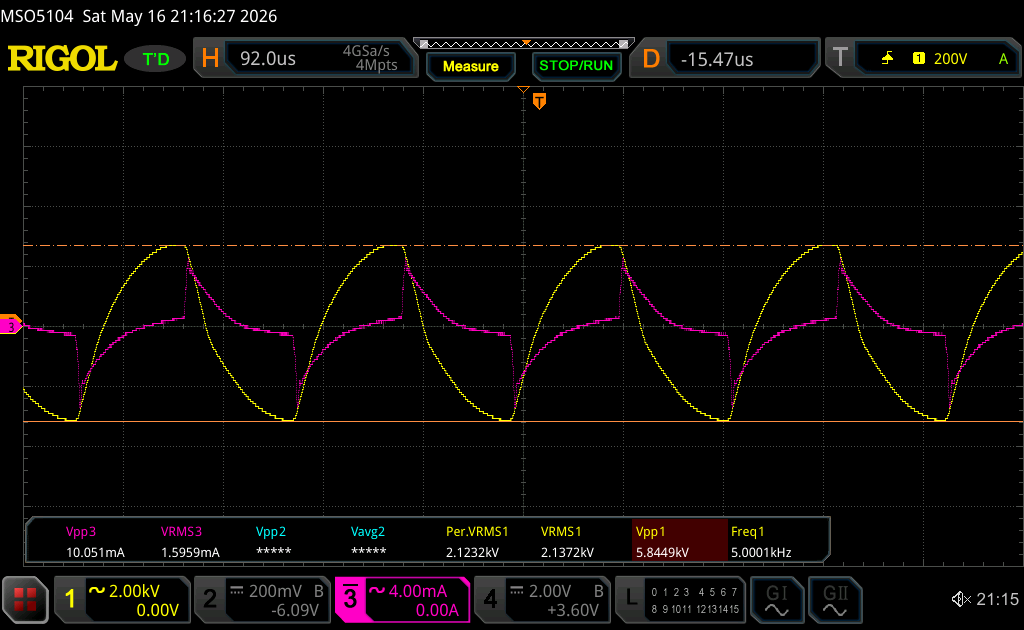
docs/Figures/Scope_Captures/not_defined_PIC_2116_16052026.png
