Teille98/HVGene-OpenHardware/docs/Figures/Component_Photos/LCD_SCREEN.png

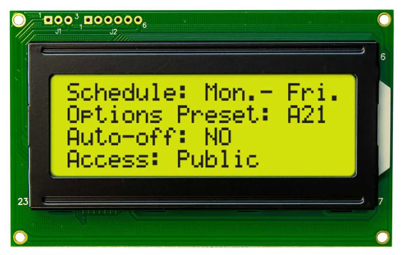
docs/Figures/Component_Photos/LCD_SCREEN.png
