Teille98/HVGene-OpenHardware/docs/Figures/Component_Photos/PCB.png

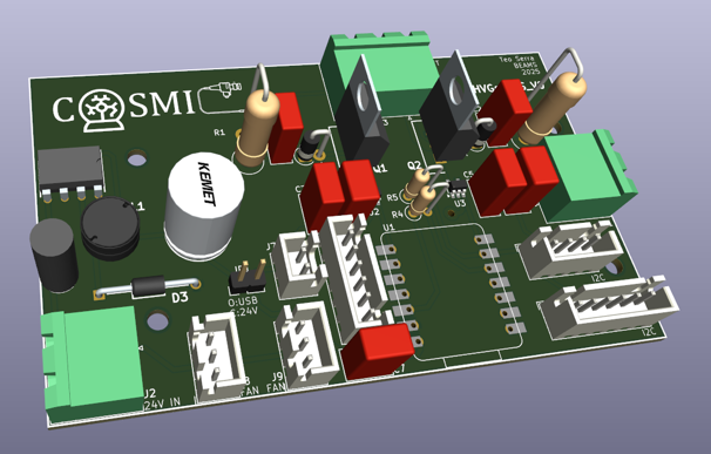
docs/Figures/Component_Photos/PCB.png
