Teille98/HVGene-OpenHardware/docs/Figures/Component_Photos/Prim_Winding_conn.png

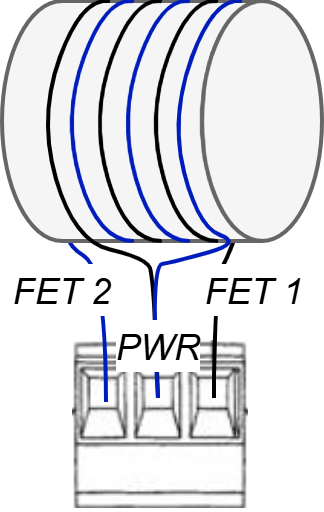
docs/Figures/Component_Photos/Prim_Winding_conn.png
