Teille98/HVGene-OpenHardware/docs/Figures/Component_Photos/ROT_ENCODER.png

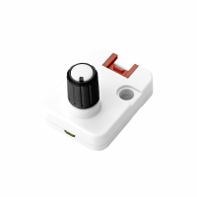
docs/Figures/Component_Photos/ROT_ENCODER.png
