Teille98/HVGene-OpenHardware/docs/Figures/Component_Photos/sm_black_top.png

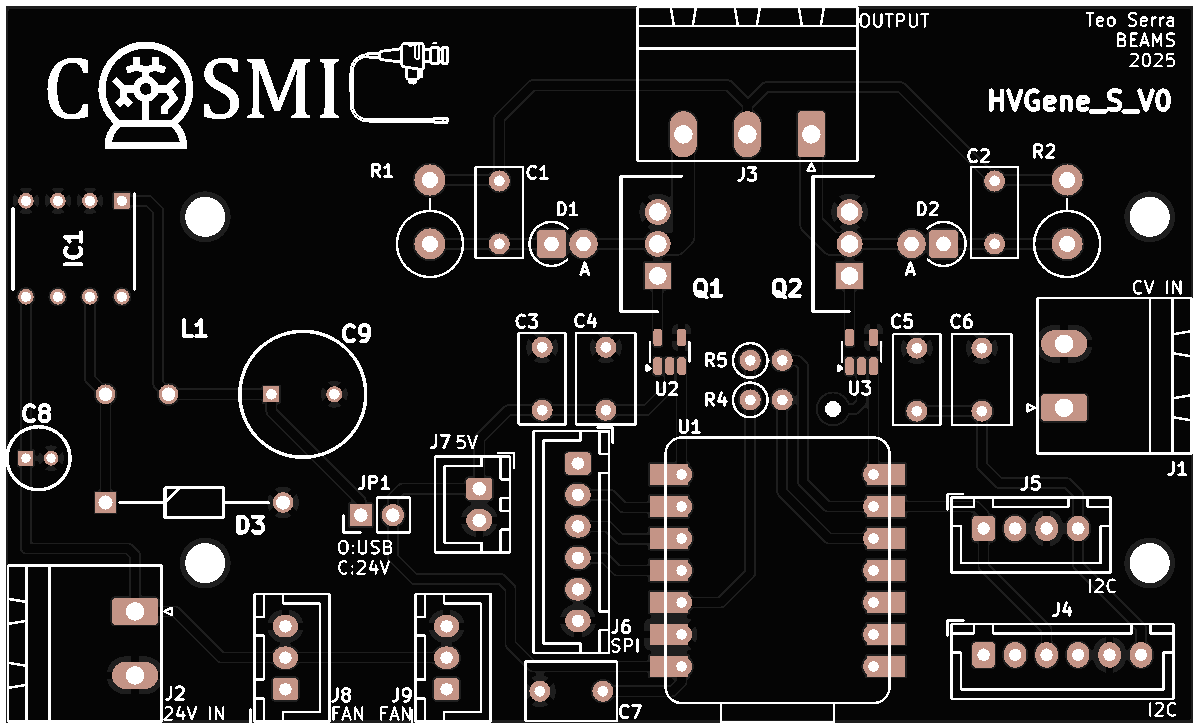
docs/Figures/Component_Photos/sm_black_top.png
