Teille98/HVGene-OpenHardware/docs/Figures/Component_Photos/TRANSFO.png

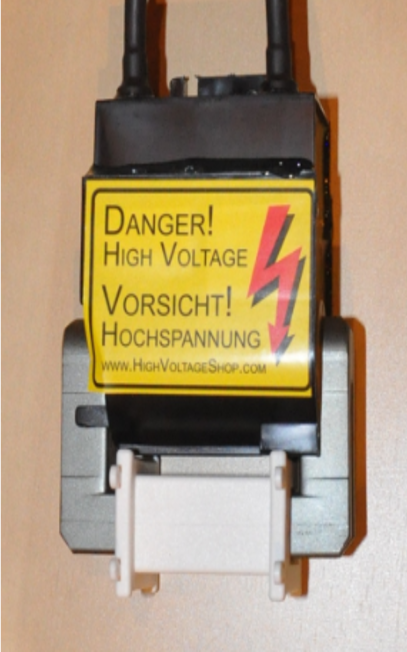
docs/Figures/Component_Photos/TRANSFO.png
