Teille98/HVGene-OpenHardware/docs/Figures/Component_Photos/TXH_240-124.png

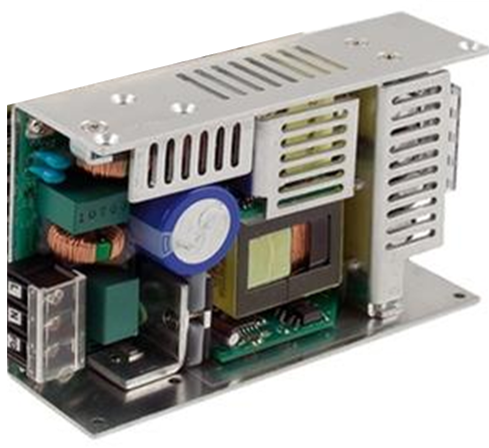
docs/Figures/Component_Photos/TXH_240-124.png
