Teille98/HVGene-OpenHardware/hardware/KiCAD/Seeeduino-XIAO-KICAD/ssw-107-01-t-s.stp

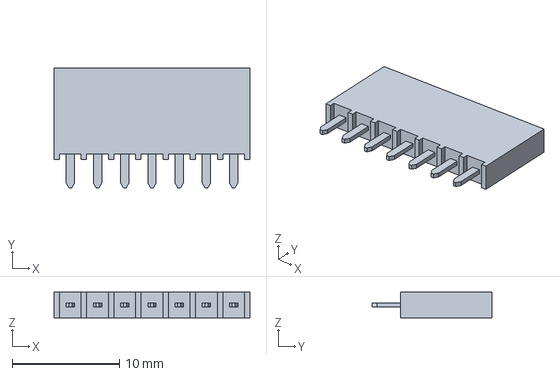
[picture p109: CAD file, 2026-08-10]
hardware/KiCAD/Seeeduino-XIAO-KICAD/ssw-107-01-t-s.stp
18.3 x 11.2 x 2.41 mm
