Teille98/HVGene-OpenHardware/hardware/CAD-Fusion360/ELEC_comp/TRANSFO.step

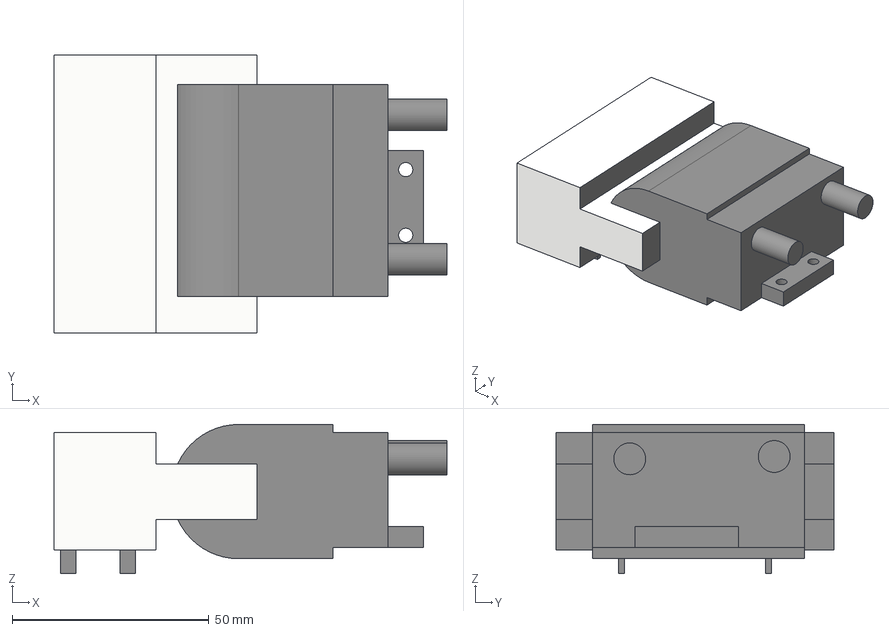
[picture p110: CAD file, 2026-08-10]
hardware/CAD-Fusion360/ELEC_comp/TRANSFO.step
100.0 x 70.6 x 37.9 mm
