Teille98/HVGene-OpenHardware/hardware/CAD-Fusion360/MECHA_comp/PLATE_HV_SIDE.step

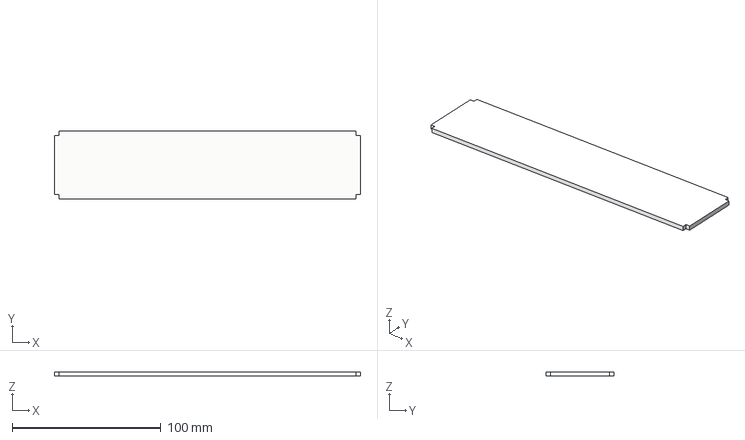
[picture p111: CAD file, 2026-08-10]
hardware/CAD-Fusion360/MECHA_comp/PLATE_HV_SIDE.step
206.0 x 46.0 x 3.00 mm
