Teille98/HVGene-OpenHardware/hardware/KiCAD/Seeeduino-XIAO-KICAD/Seeed Studio XIAO RP2040 v26.step

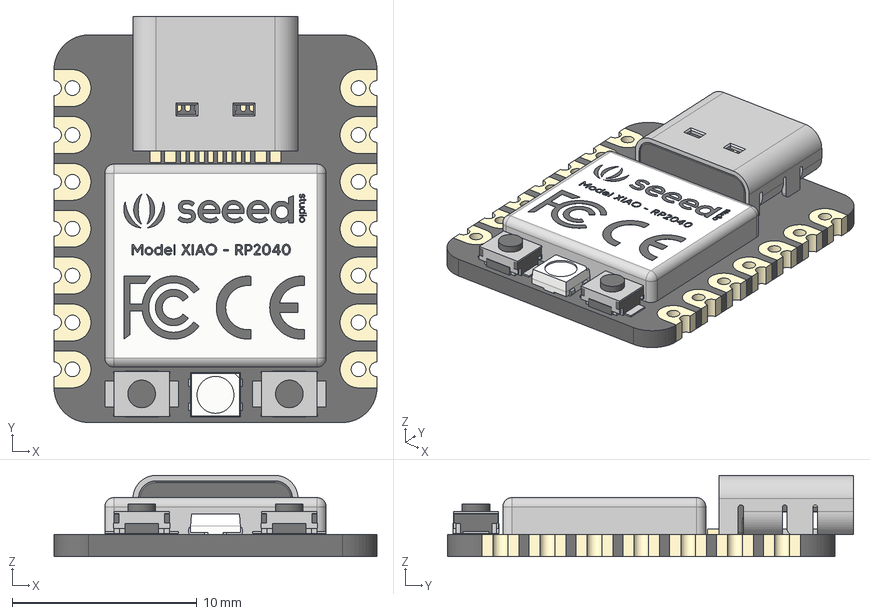
[picture p112: CAD file, 2026-08-10]
hardware/KiCAD/Seeeduino-XIAO-KICAD/Seeed Studio XIAO RP2040 v26.step
17.5 x 22.0 x 4.40 mm
type-c v2
smd_button v3
DOUT
DIN
VSS
VDD
smd_button v3(Mirror)
