Teille98/HVGene-OpenHardware/hardware/KiCAD/Seeeduino-XIAO-KICAD/xiao_rp2040-main/xiao_rp2040-main/Pin.FCStd

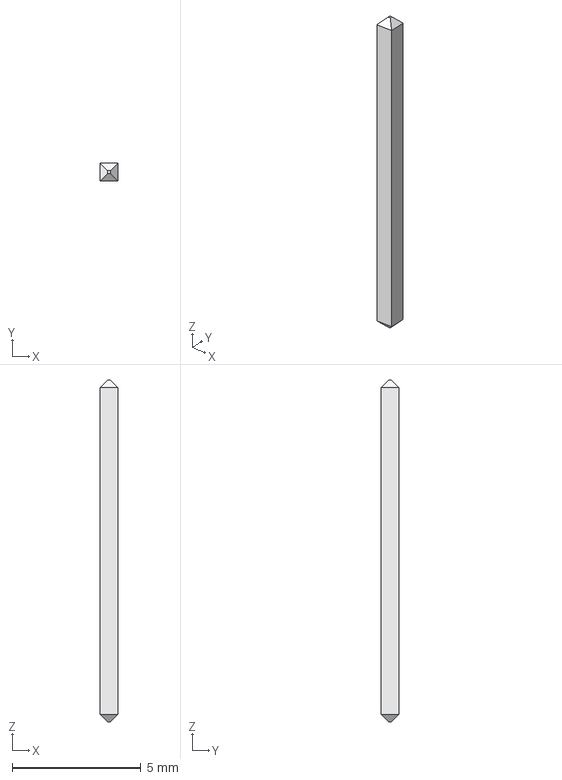
[picture p113: CAD file, 2026-08-10]
hardware/KiCAD/Seeeduino-XIAO-KICAD/xiao_rp2040-main/xiao_rp2040-main/Pin.FCStd
0.7 x 0.7 x 13.3 mm
