Teille98/HVGene-OpenHardware/hardware/CAD-Fusion360/ELEC_comp/LCD_SCREEN.step

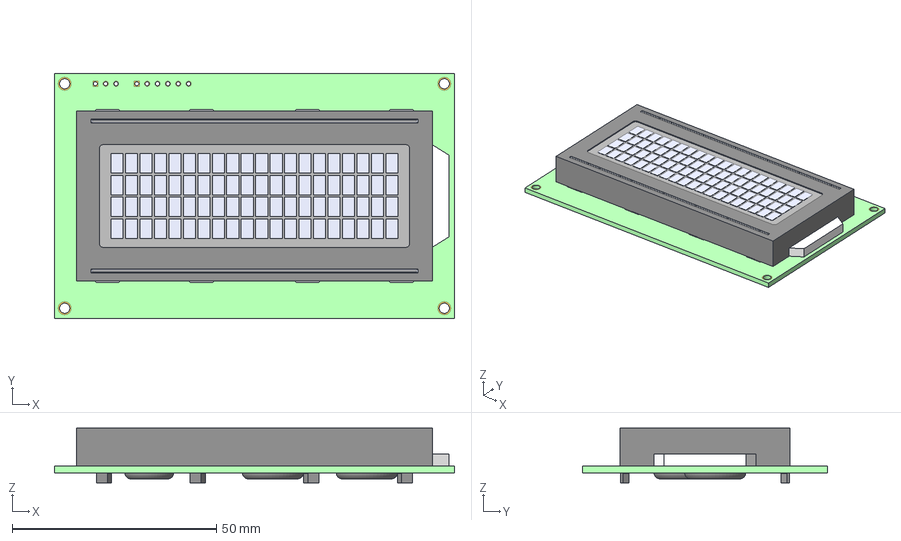
[picture p114: CAD file, 2026-08-10]
hardware/CAD-Fusion360/ELEC_comp/LCD_SCREEN.step
98.0 x 60.0 x 13.4 mm
