Teille98/HVGene-OpenHardware/hardware/KiCAD/Seeeduino-XIAO-KICAD/xiao_rp2040-main/xiao_rp2040-main/SocketPin.FCStd

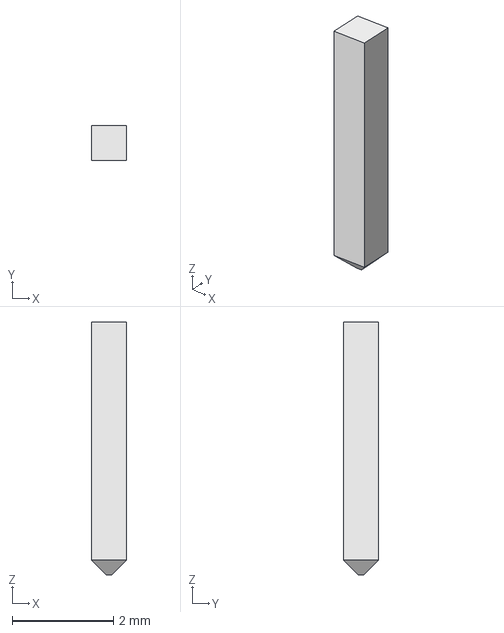
[picture p115: CAD file, 2026-08-10]
hardware/KiCAD/Seeeduino-XIAO-KICAD/xiao_rp2040-main/xiao_rp2040-main/SocketPin.FCStd
0.7 x 0.7 x 5.00 mm
