Teille98/HVGene-OpenHardware/hardware/CAD-Fusion360/ELEC_comp/FAN_80mm.step

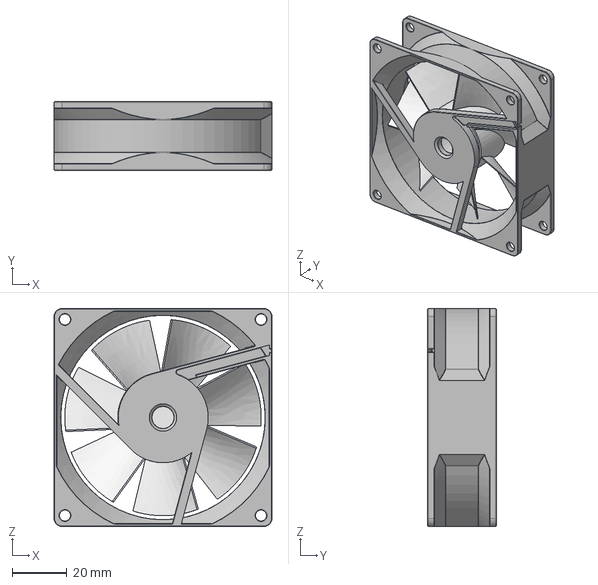
[picture p116: CAD file, 2026-08-10]
hardware/CAD-Fusion360/ELEC_comp/FAN_80mm.step
79.5 x 25.0 x 79.5 mm
80MM_FAN_PROP
80MM_FAN_HOUSING
