Teille98/HVGene-OpenHardware/hardware/CAD-Fusion360/ELEC_comp/TERM_BLOCK_2POS.step

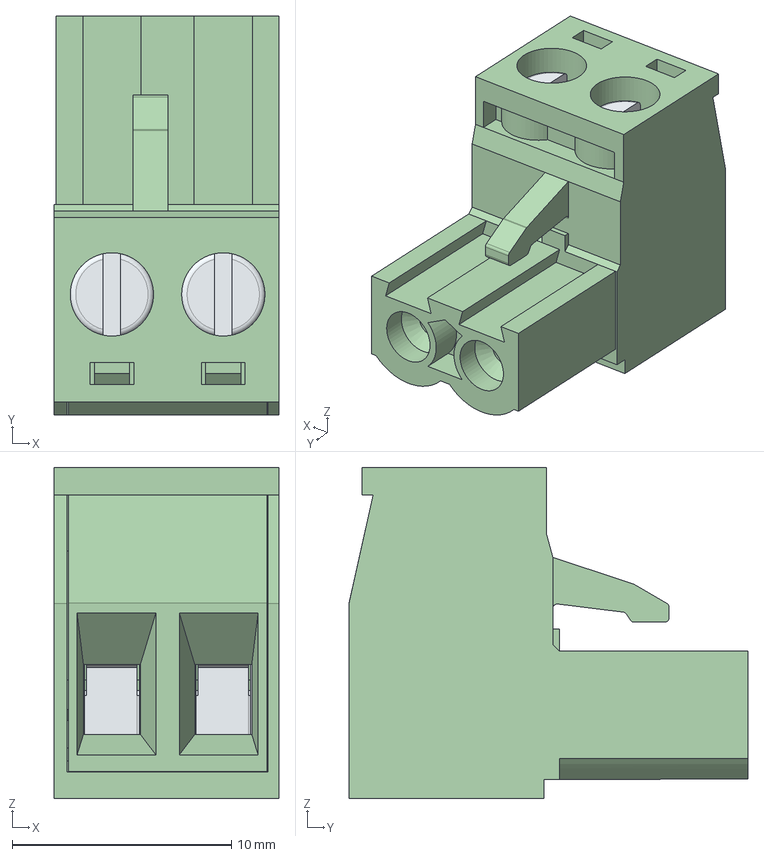
[picture p118: CAD file, 2026-08-10]
hardware/CAD-Fusion360/ELEC_comp/TERM_BLOCK_2POS.step
10.3 x 18.2 x 15.1 mm
6913515000xx_CAGE x 2
6913515000xx_PIN x 2
6913515000xx_VIS x 2
691351500002_CAPOT
