Teille98/HVGene-OpenHardware/hardware/CAD-Fusion360/MECHA_comp/MakerBeam_TNUT_10x10mm.step

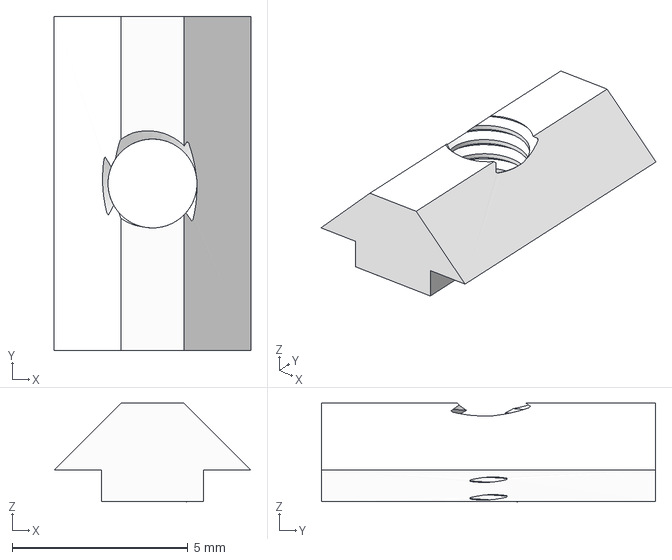
[picture p119: CAD file, 2026-08-10]
hardware/CAD-Fusion360/MECHA_comp/MakerBeam_TNUT_10x10mm.step
5.60 x 9.50 x 2.80 mm
