Teille98/HVGene-OpenHardware/hardware/KiCAD/Seeeduino-XIAO-KICAD/xiao_rp2040-main/xiao_rp2040-main/SocketBody.FCStd

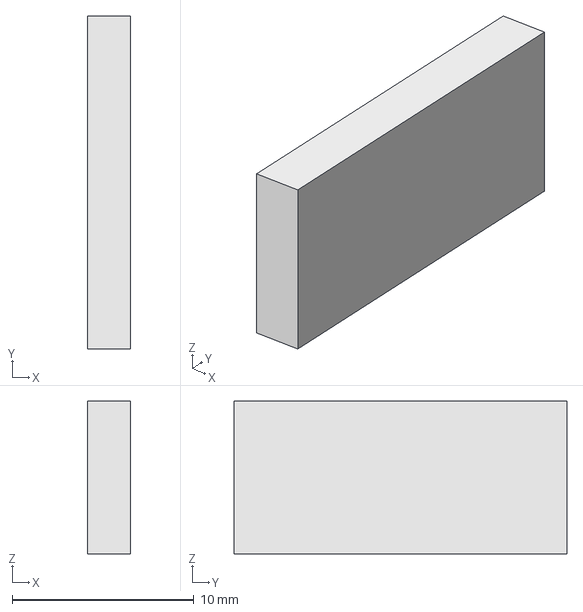
[picture p120: CAD file, 2026-08-10]
hardware/KiCAD/Seeeduino-XIAO-KICAD/xiao_rp2040-main/xiao_rp2040-main/SocketBody.FCStd
2.39 x 18.3 x 8.40 mm
