Teille98/HVGene-OpenHardware/hardware/CAD-Fusion360/ELEC_comp/LCD_BUCK_MODULE.step

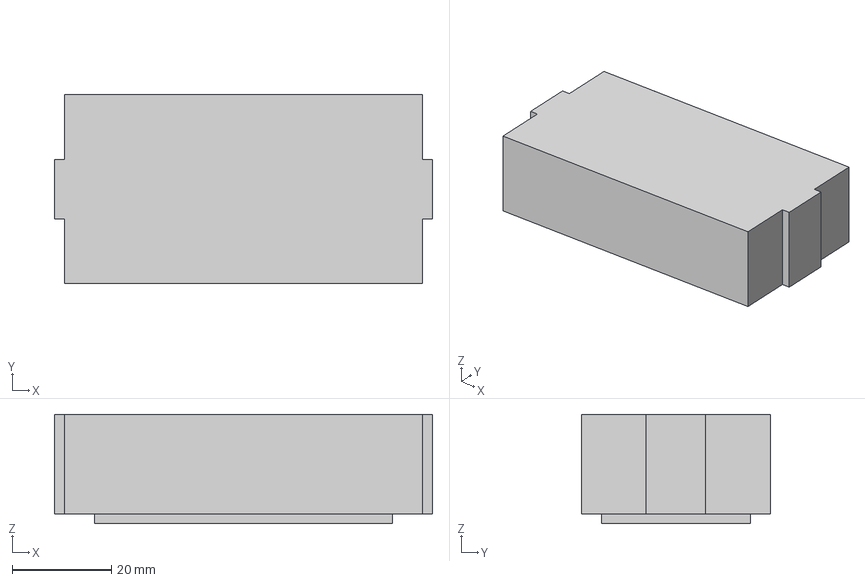
[picture p121: CAD file, 2026-08-10]
hardware/CAD-Fusion360/ELEC_comp/LCD_BUCK_MODULE.step
76.0 x 38.0 x 22.0 mm
