Teille98/HVGene-OpenHardware/hardware/KiCAD/Seeeduino-XIAO-KICAD/xiao_rp2040-main/xiao_rp2040-main/LED.FCStd

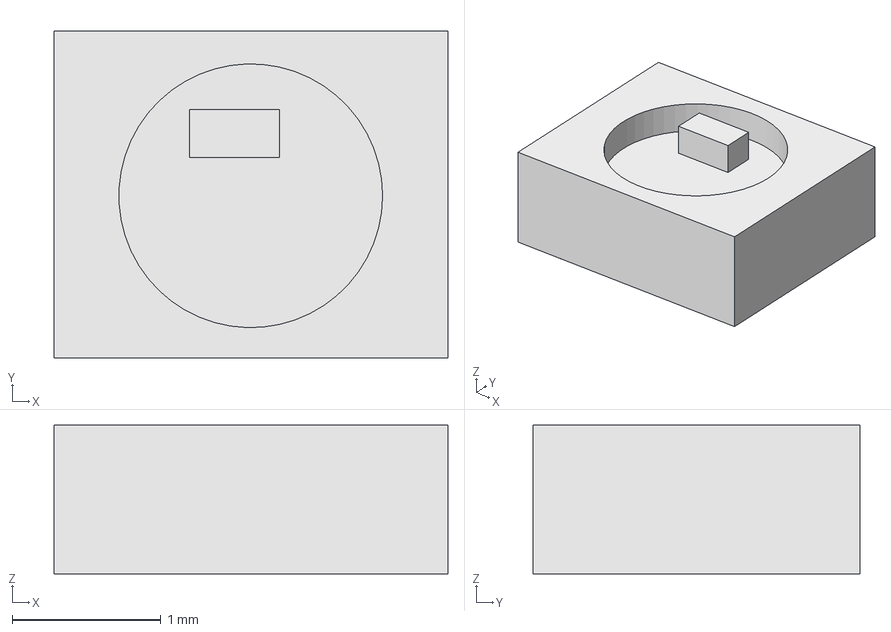
[picture p123: CAD file, 2026-08-10]
hardware/KiCAD/Seeeduino-XIAO-KICAD/xiao_rp2040-main/xiao_rp2040-main/LED.FCStd
2.65 x 2.20 x 1.00 mm
