Teille98/HVGene-OpenHardware/hardware/CAD-Fusion360/ELEC_comp/TERM_BLOCK_3POS.step

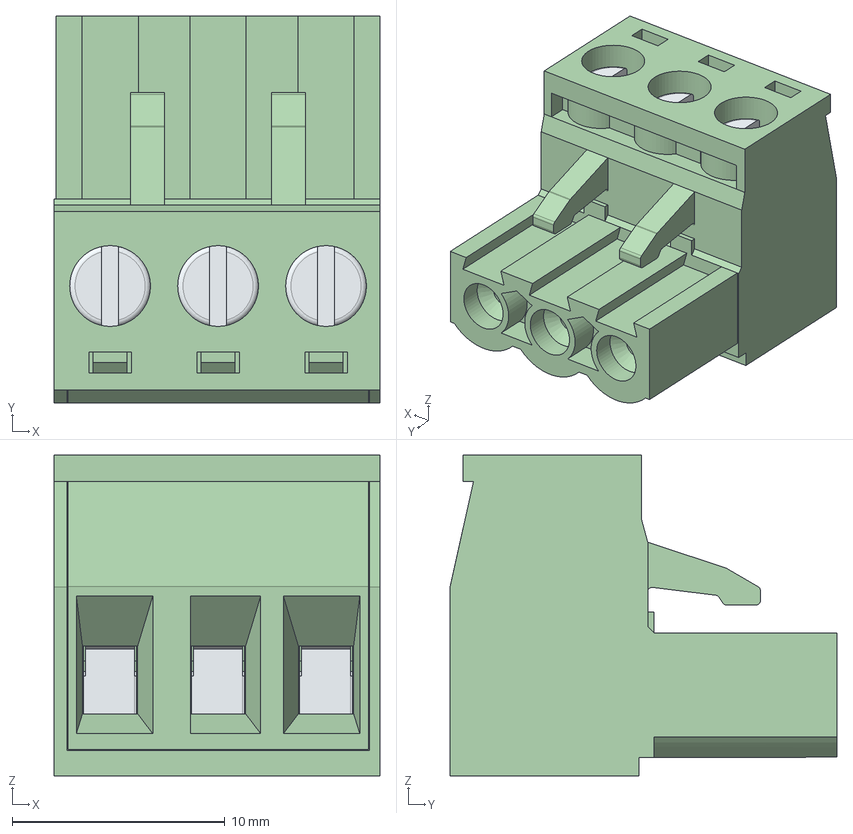
[picture p124: CAD file, 2026-08-10]
hardware/CAD-Fusion360/ELEC_comp/TERM_BLOCK_3POS.step
15.3 x 18.2 x 15.1 mm
6913515000xx_CAGE x 3
6913515000xx_PIN x 3
6913515000xx_VIS x 3
691351500003_CAPOT
