Teille98/HVGene-OpenHardware/hardware/CAD-Fusion360/MECHA_comp/PLATE_LV_SIDE.step

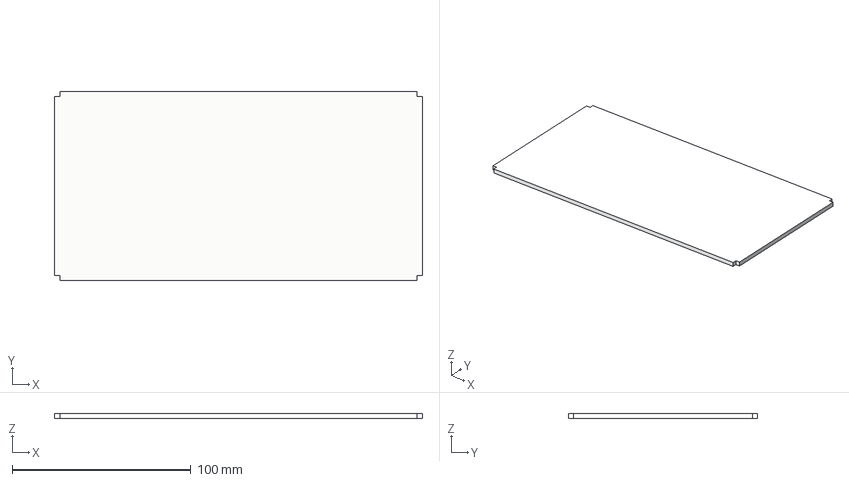
[picture p125: CAD file, 2026-08-10]
hardware/CAD-Fusion360/MECHA_comp/PLATE_LV_SIDE.step
206.0 x 106.0 x 3.00 mm
