Teille98/HVGene-OpenHardware/hardware/KiCAD/Seeeduino-XIAO-KICAD/xiao_rp2040-main/xiao_rp2040-main/USBC2.FCStd

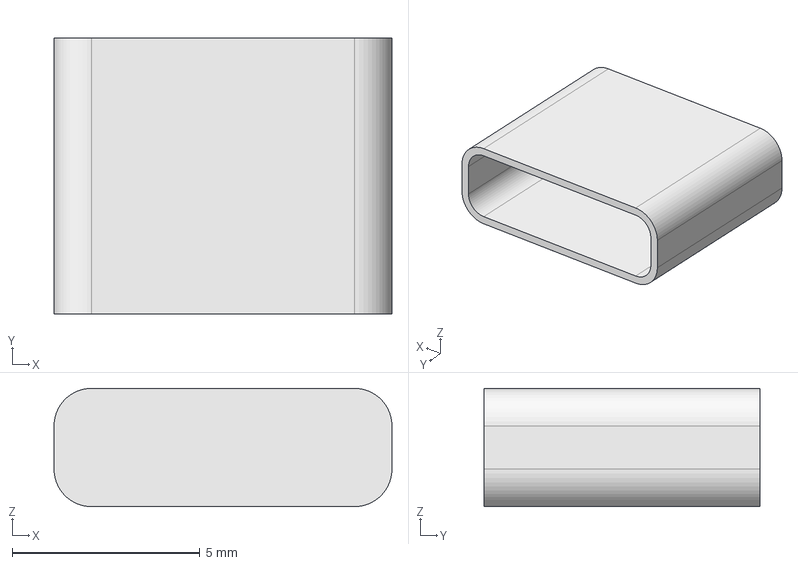
[picture p126: CAD file, 2026-08-10]
hardware/KiCAD/Seeeduino-XIAO-KICAD/xiao_rp2040-main/xiao_rp2040-main/USBC2.FCStd
9.00 x 7.35 x 3.15 mm
