Teille98/HVGene-OpenHardware/hardware/CAD-Fusion360/MECHA_comp/MakerBeam_HINGE_AXE.step

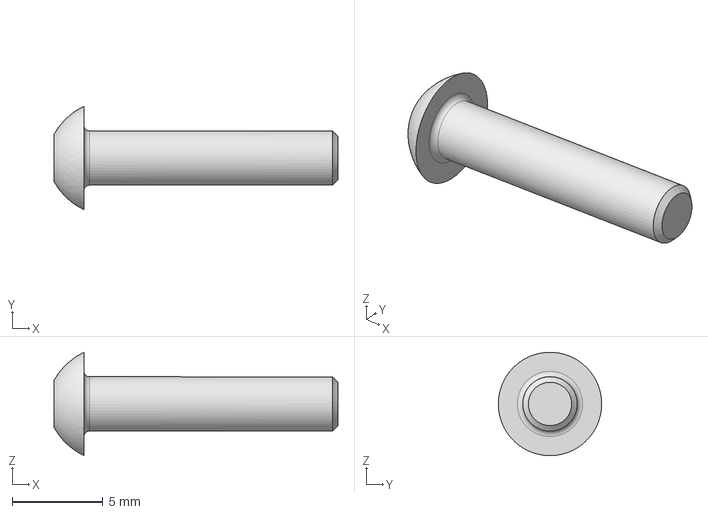
[picture p127: CAD file, 2026-08-10]
hardware/CAD-Fusion360/MECHA_comp/MakerBeam_HINGE_AXE.step
15.7 x 5.70 x 5.69 mm
