Teille98/HVGene-OpenHardware/hardware/CAD-Fusion360/ELEC_comp/BUCK_MODULE.step

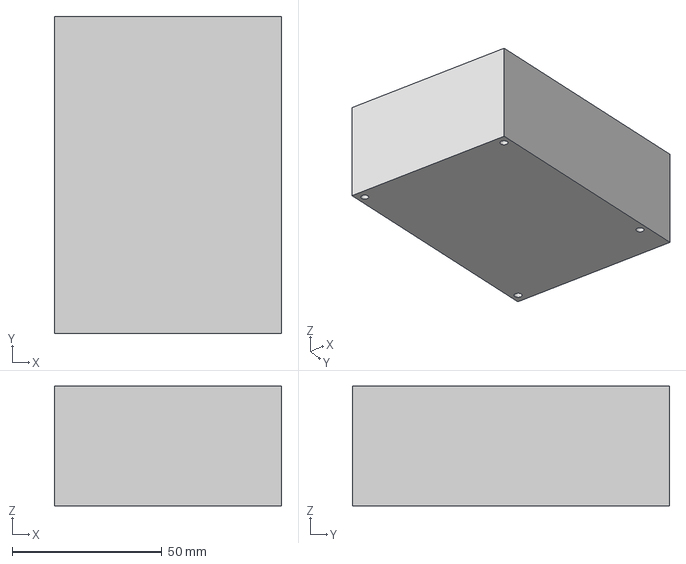
[picture p129: CAD file, 2026-08-10]
hardware/CAD-Fusion360/ELEC_comp/BUCK_MODULE.step
76.0 x 106.0 x 40.0 mm
