Teille98/HVGene-OpenHardware/hardware/CAD-Fusion360/MECHA_comp/MakerBeam_PROFILE_10x10x150mm.step

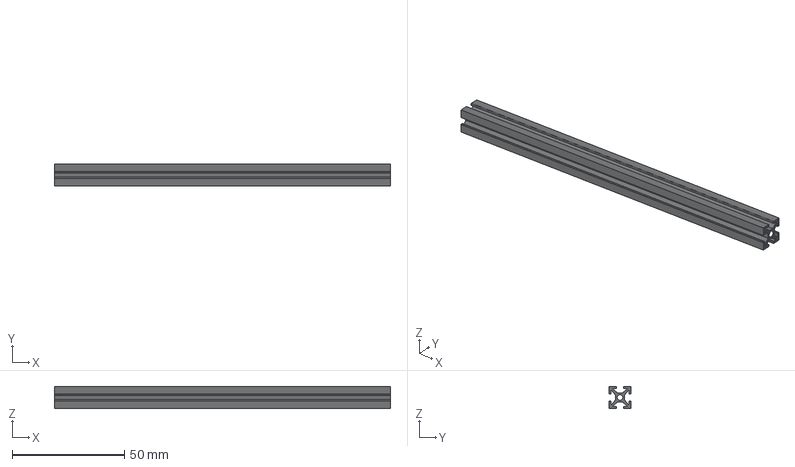
[picture p130: CAD file, 2026-08-10]
hardware/CAD-Fusion360/MECHA_comp/MakerBeam_PROFILE_10x10x150mm.step
150.0 x 10.0 x 10.0 mm
