Teille98/HVGene-OpenHardware/hardware/CAD-Fusion360/MECHA_comp/PLATE_HV_TOP.step

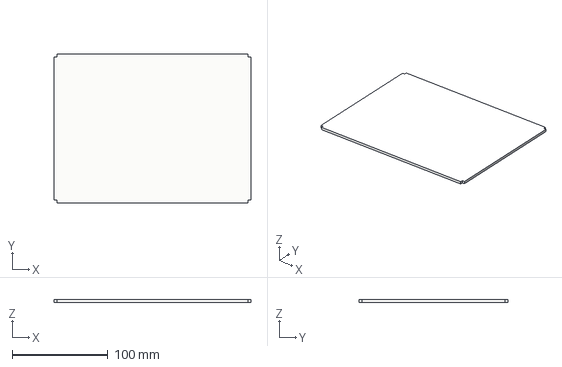
[picture p131: CAD file, 2026-08-10]
hardware/CAD-Fusion360/MECHA_comp/PLATE_HV_TOP.step
206.0 x 156.0 x 3.00 mm
