Teille98/HVGene-OpenHardware/hardware/KiCAD/Seeeduino-XIAO-KICAD/xiao_rp2040-main/xiao_rp2040-main/Socket.FCStd

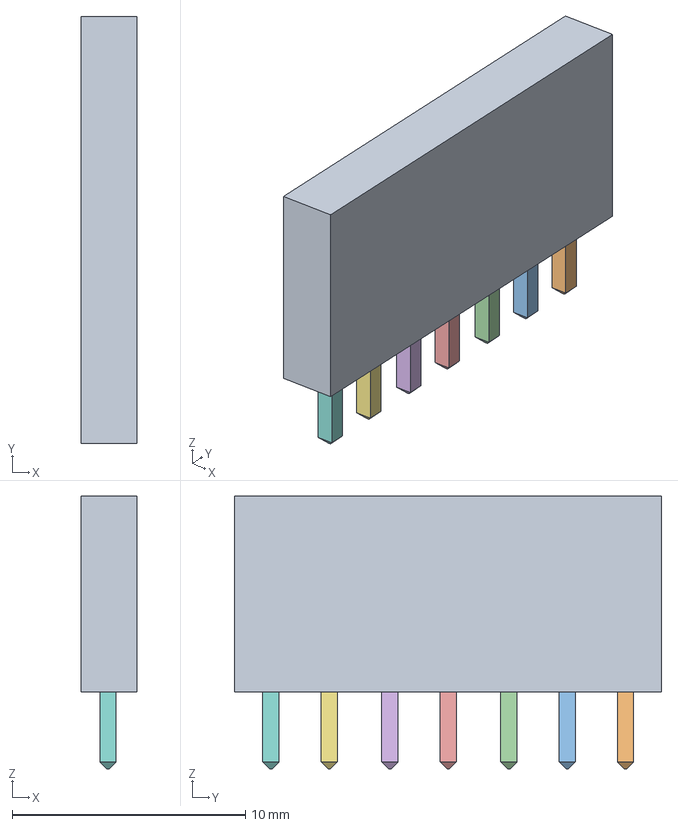
[picture p132: CAD file, 2026-08-10]
hardware/KiCAD/Seeeduino-XIAO-KICAD/xiao_rp2040-main/xiao_rp2040-main/Socket.FCStd
2.39 x 18.3 x 11.7 mm
SocketBody_001
SocketPin_001
SocketPin_002
SocketPin_003
SocketPin_004
SocketPin_005
SocketPin_006
SocketPin_007
