Teille98/HVGene-OpenHardware/hardware/CAD-Fusion360/MECHA_comp/MakerBeam_PROFILE_10x10x100mm.step

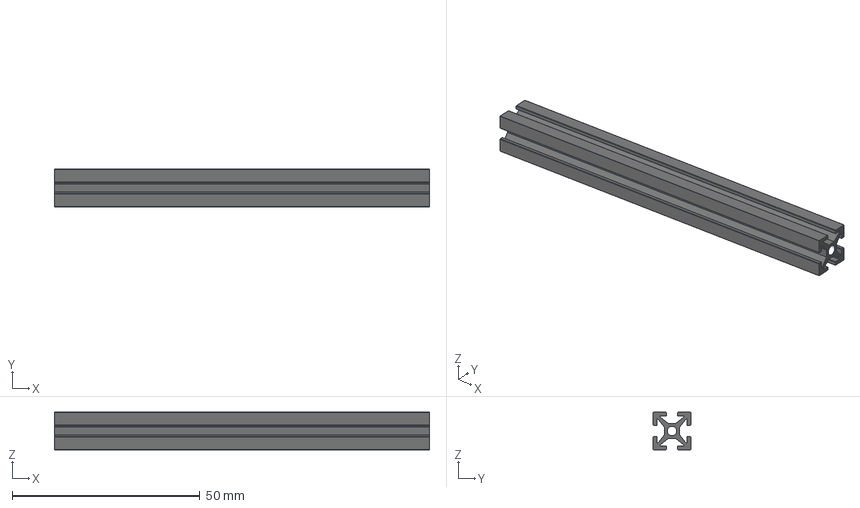
[picture p133: CAD file, 2026-08-10]
hardware/CAD-Fusion360/MECHA_comp/MakerBeam_PROFILE_10x10x100mm.step
100.0 x 10.0 x 10.0 mm
