Teille98/HVGene-OpenHardware/hardware/CAD-Fusion360/MECHA_comp/MakerBeam_HINGE_PIECE.step

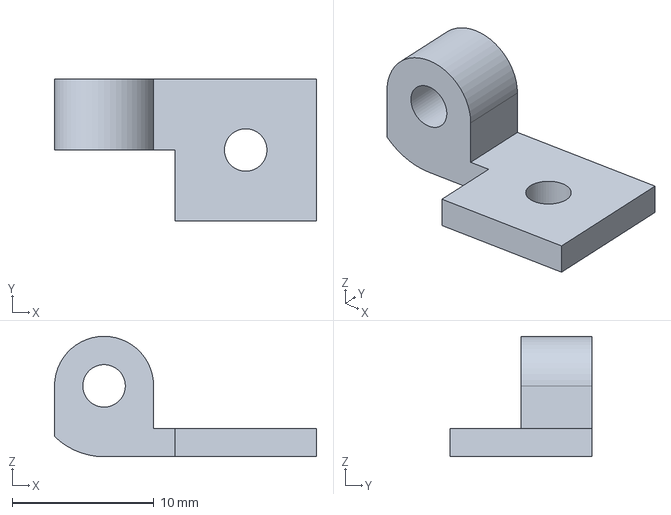
[picture p136: CAD file, 2026-08-10]
hardware/CAD-Fusion360/MECHA_comp/MakerBeam_HINGE_PIECE.step
18.5 x 10.0 x 8.50 mm
