Teille98/HVGene-OpenHardware/hardware/CAD-Fusion360/MECHA_comp/MakerBeam_HINGE_LOCKNUT.step

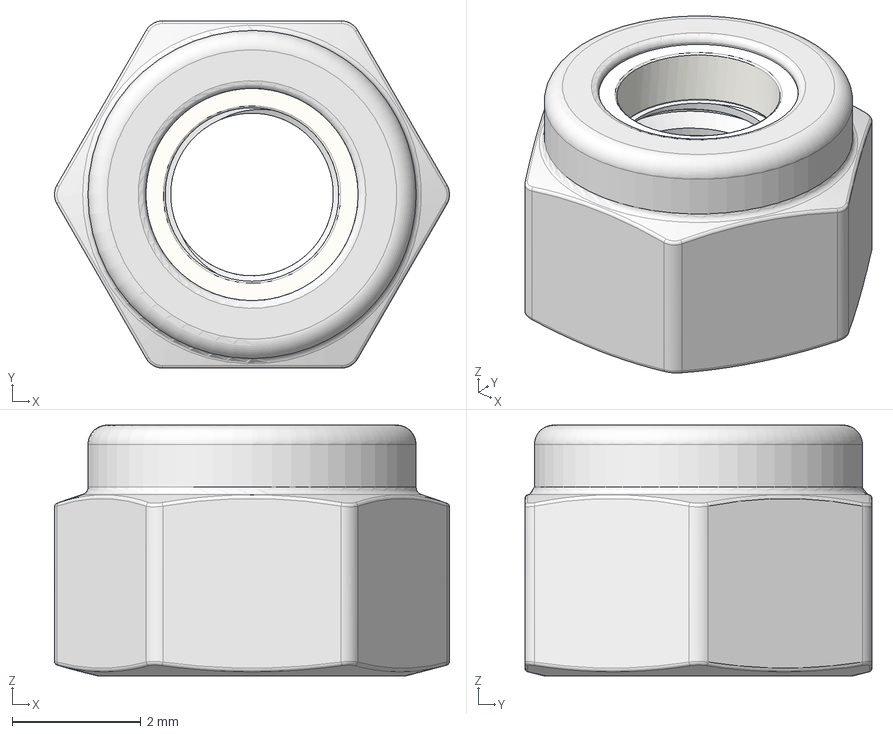
[picture p137: CAD file, 2026-08-10]
hardware/CAD-Fusion360/MECHA_comp/MakerBeam_HINGE_LOCKNUT.step
6.14 x 5.40 x 3.90 mm
