Teille98/HVGene-OpenHardware/hardware/CAD-Fusion360/MECHA_comp/PLATE_LV_BACK.step

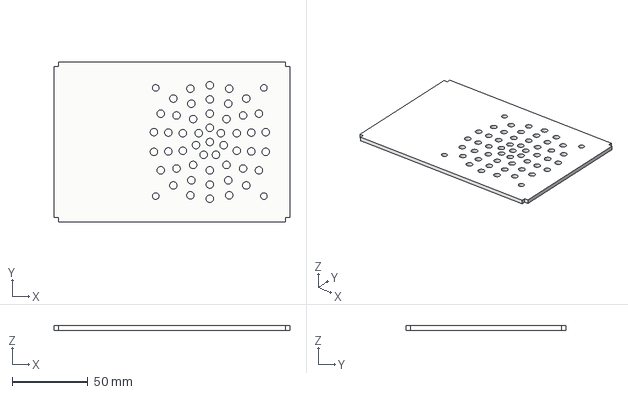
[picture p139: CAD file, 2026-08-10]
hardware/CAD-Fusion360/MECHA_comp/PLATE_LV_BACK.step
156.0 x 106.0 x 3.00 mm
