Teille98/HVGene-OpenHardware/hardware/CAD-Fusion360/MECHA_comp/MakerBeam_PROFILE_10x10x200mm.step

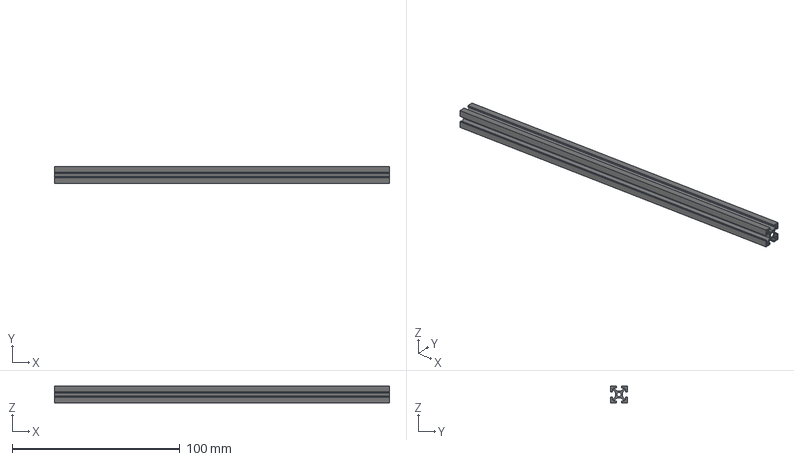
[picture p140: CAD file, 2026-08-10]
hardware/CAD-Fusion360/MECHA_comp/MakerBeam_PROFILE_10x10x200mm.step
200.0 x 10.0 x 10.0 mm
