Teille98/HVGene-OpenHardware/hardware/CAD-Fusion360/MECHA_comp/MakerBeam_CUBE_CORNER_10x10x10mm.step

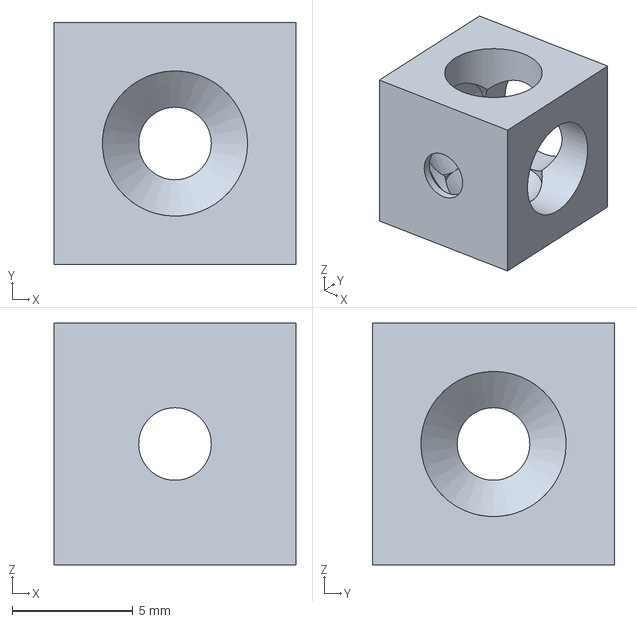
[picture p141: CAD file, 2026-08-10]
hardware/CAD-Fusion360/MECHA_comp/MakerBeam_CUBE_CORNER_10x10x10mm.step
10.0 x 10.0 x 10.0 mm
