Teille98/HVGene-OpenHardware/hardware/CAD-Fusion360/MECHA_comp/MakerBeam_PROFILE_10x10x40mm.step

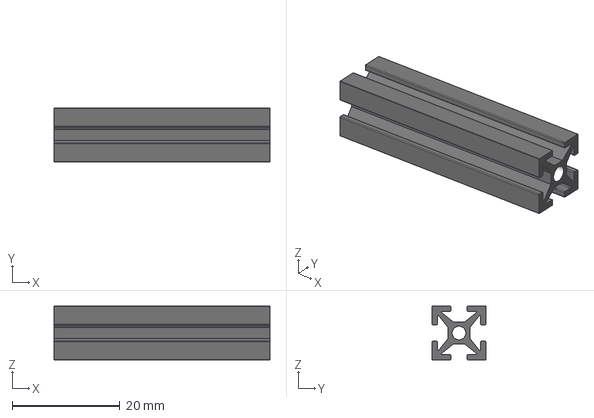
[picture p143: CAD file, 2026-08-10]
hardware/CAD-Fusion360/MECHA_comp/MakerBeam_PROFILE_10x10x40mm.step
40.0 x 10.0 x 10.0 mm
