Teille98/HVGene-OpenHardware/hardware/CAD-Fusion360/MECHA_comp/HEATSINK.step

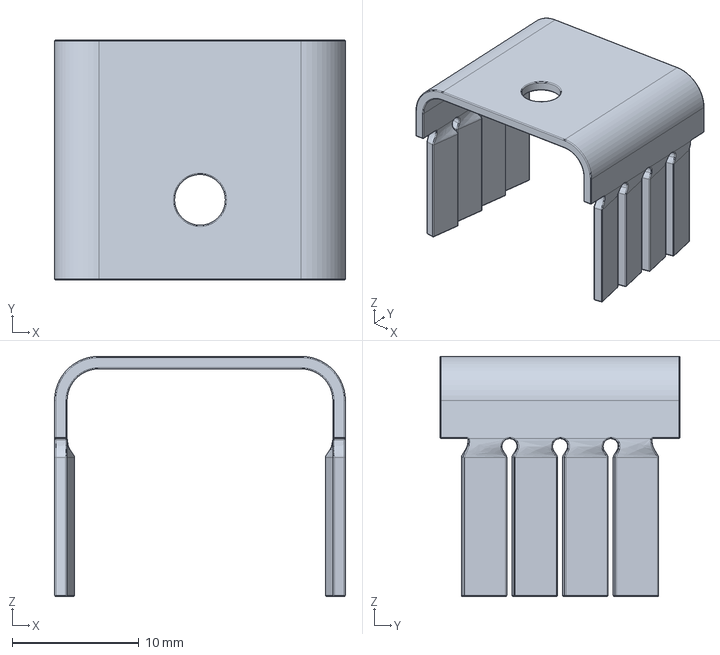
[picture p144: CAD file, 2026-08-10]
hardware/CAD-Fusion360/MECHA_comp/HEATSINK.step
23.0 x 19.0 x 19.0 mm
