Teille98/HVGene-OpenHardware/hardware/CAD-Fusion360/MECHA_comp/STANDOFF_M3_5mm.step

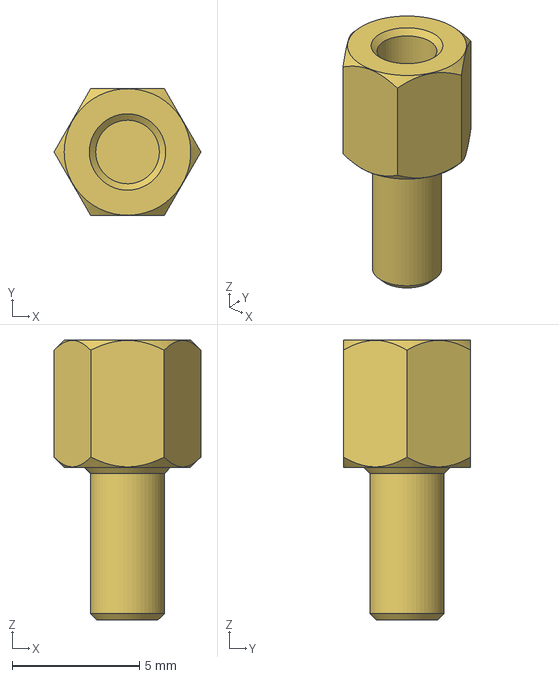
[picture p145: CAD file, 2026-08-10]
hardware/CAD-Fusion360/MECHA_comp/STANDOFF_M3_5mm.step
5.77 x 5.00 x 11.0 mm
