Teille98/HVGene-OpenHardware/hardware/CAD-Fusion360/MECHA_comp/PLATE_LV_FRONT.step

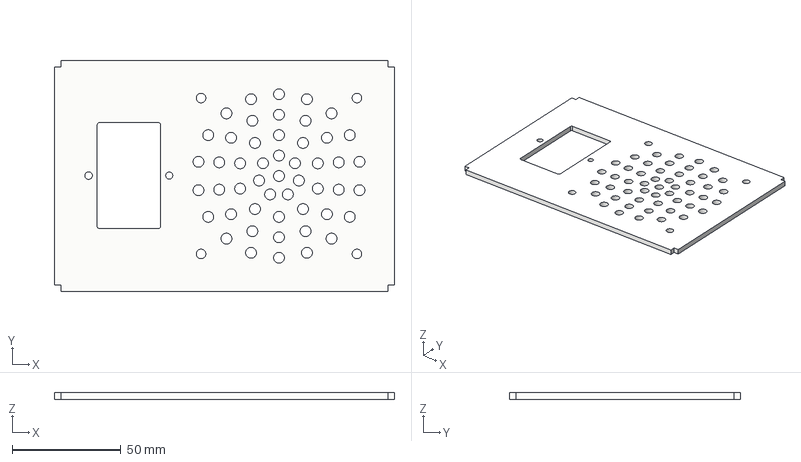
[picture p146: CAD file, 2026-08-10]
hardware/CAD-Fusion360/MECHA_comp/PLATE_LV_FRONT.step
156.0 x 106.0 x 3.00 mm
