Teille98/HVGene-OpenHardware/docs/Figures/Article_Figures/Fig_Val7_OperatingMap.png

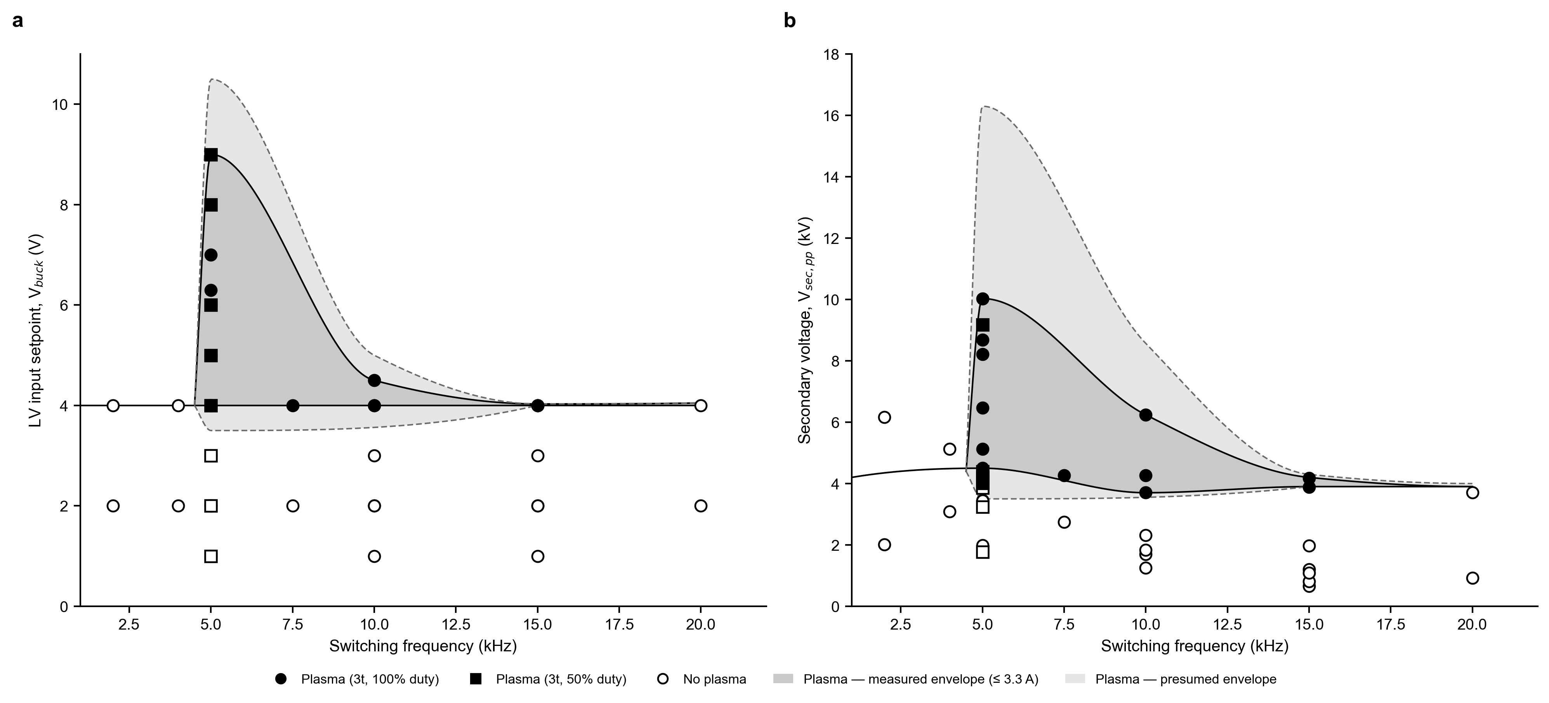
docs/Figures/Article_Figures/Fig_Val7_OperatingMap.png
