Teille98/HVGene-OpenHardware/docs/Figures/Article_Figures/Mechanical_Assembly_Exploded_Views.png

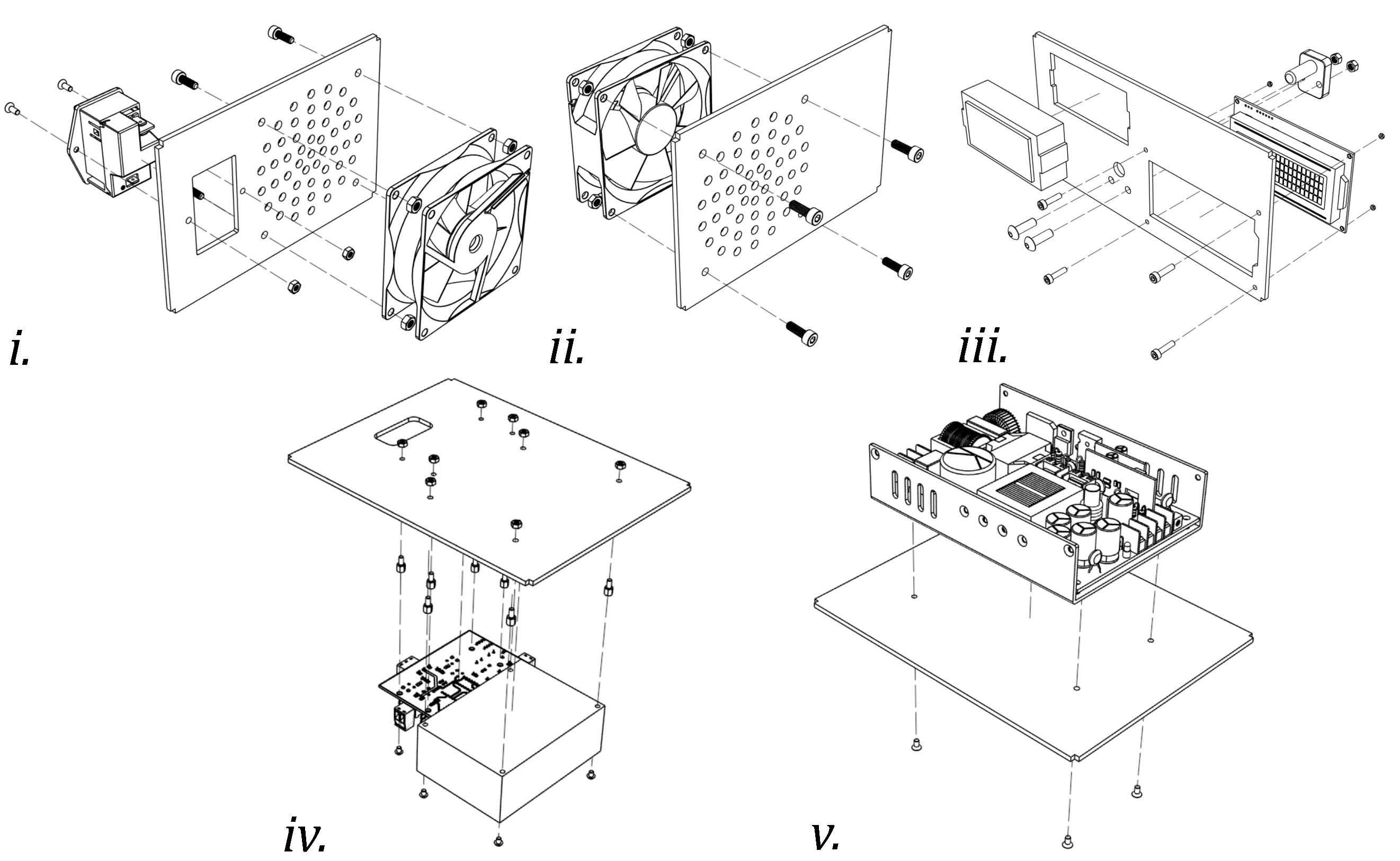
docs/Figures/Article_Figures/Mechanical_Assembly_Exploded_Views.png
