Teille98/HVGene-OpenHardware/docs/Figures/Article_Figures/PCB_Assembled_Photo_v1_NoHeatsinks.jpeg

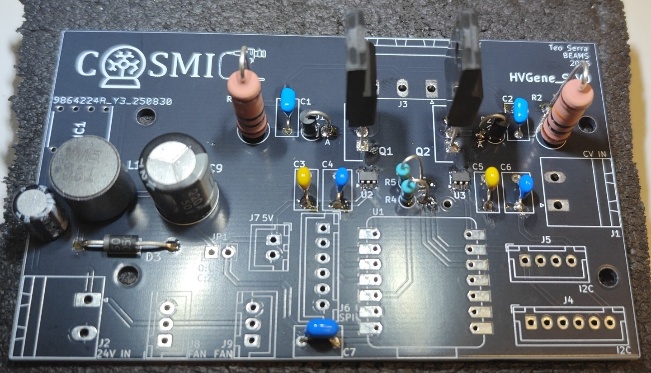
docs/Figures/Article_Figures/PCB_Assembled_Photo_v1_NoHeatsinks.jpeg
