Teille98/HVGene-OpenHardware/docs/Figures/Article_Figures/PCB_Assembled_Photo_v2_WithHeatsinks.jpeg

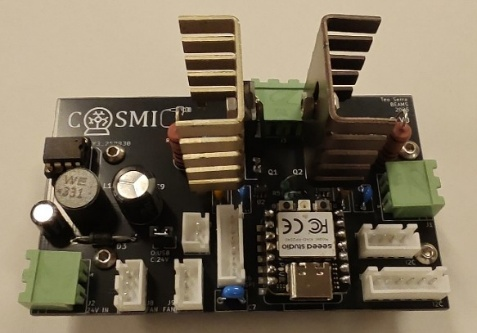
docs/Figures/Article_Figures/PCB_Assembled_Photo_v2_WithHeatsinks.jpeg
