Teille98/HVGene-OpenHardware/docs/Figures/Build_Steps/PCB_step1&2.jpg

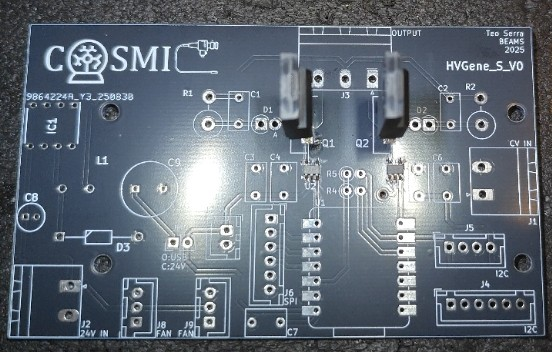
docs/Figures/Build_Steps/PCB_step1&2.jpg
