Teille98/HVGene-OpenHardware/docs/Figures/Build_Steps/PCB_step7.jpg

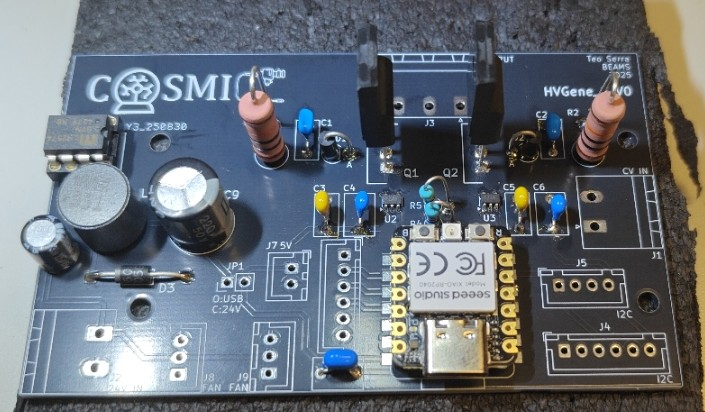
docs/Figures/Build_Steps/PCB_step7.jpg
