Teille98/HVGene-OpenHardware/docs/Figures/Build_Steps/PCB_step8.jpg

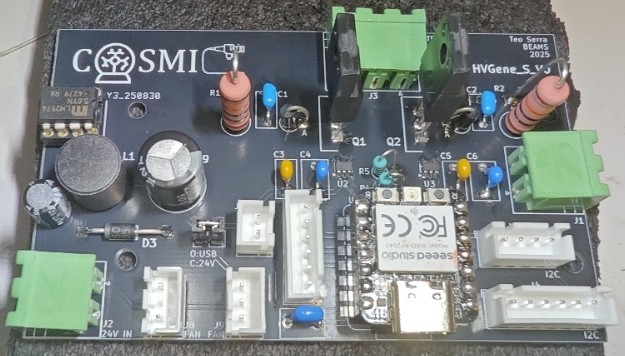
docs/Figures/Build_Steps/PCB_step8.jpg
