Teille98/HVGene-OpenHardware/docs/Figures/CAD_Renders/HV_assemb_step_2.png

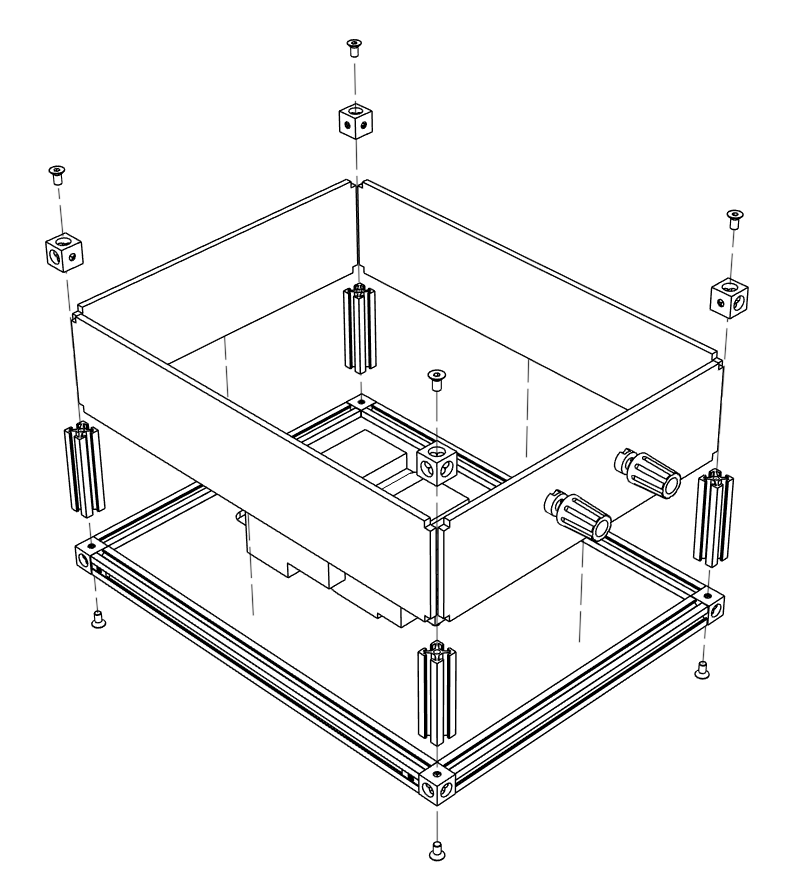
docs/Figures/CAD_Renders/HV_assemb_step_2.png
