Teille98/HVGene-OpenHardware/docs/Figures/CAD_Renders/LV_STEP_1.png

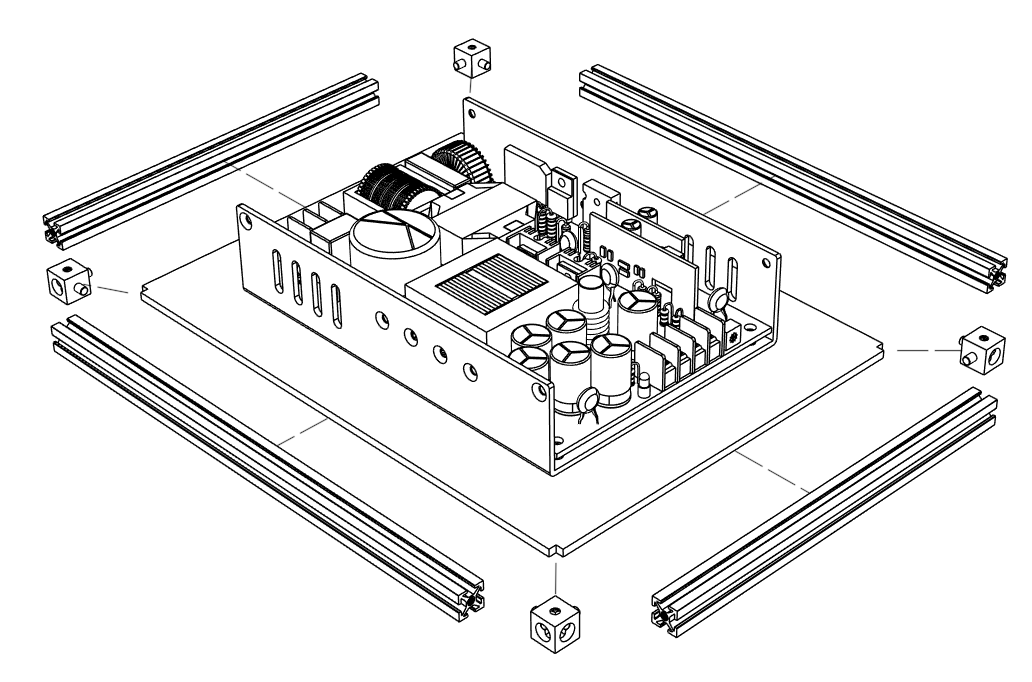
docs/Figures/CAD_Renders/LV_STEP_1.png
