Teille98/HVGene-OpenHardware/docs/Figures/CAD_Renders/LV_STEP_2.png

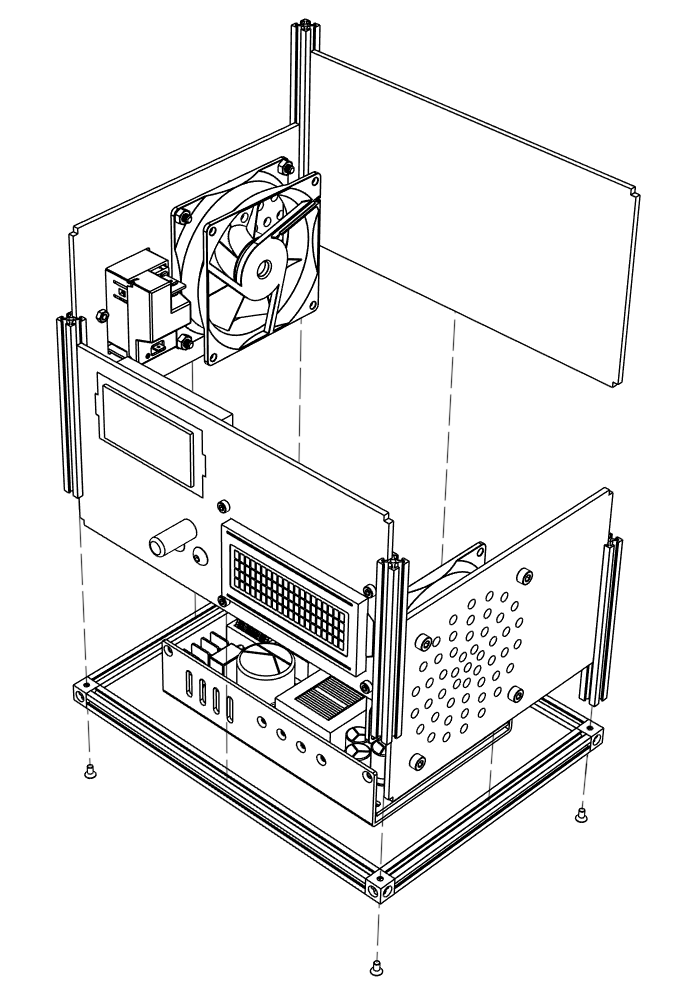
docs/Figures/CAD_Renders/LV_STEP_2.png
