Teille98/HVGene-OpenHardware/docs/Figures/CAD_Renders/LV_STEP_3.png

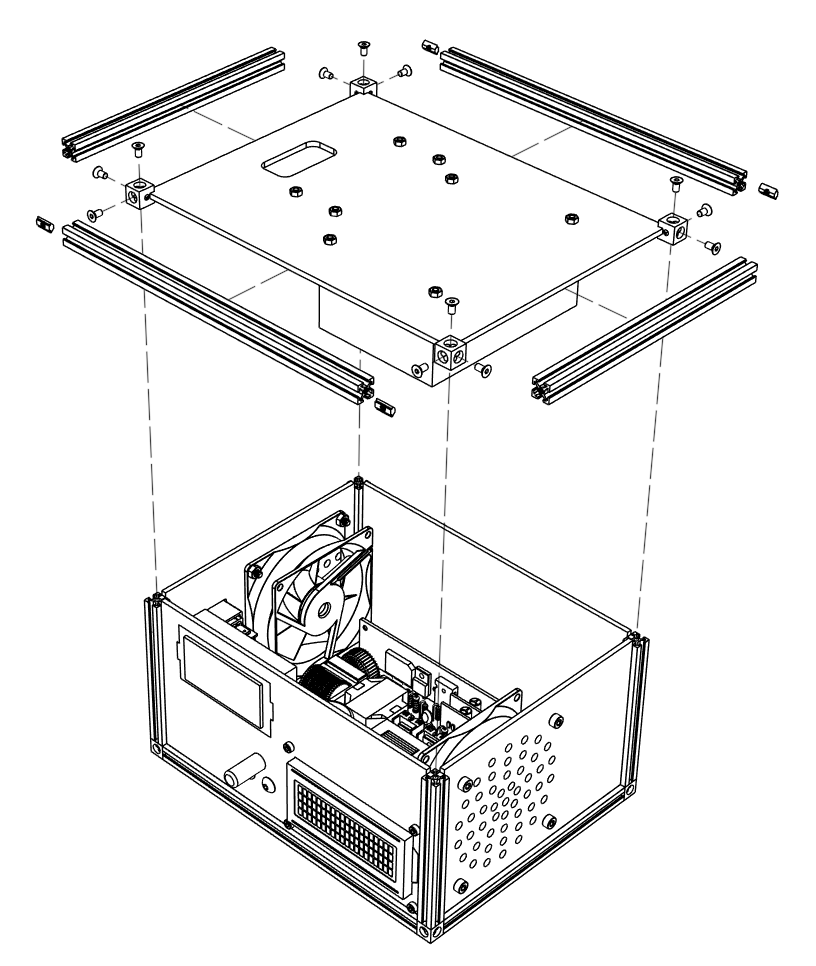
docs/Figures/CAD_Renders/LV_STEP_3.png
