Teille98/HVGene-OpenHardware/docs/Figures/Setup_Photos/current_amplifier_probe.jpg

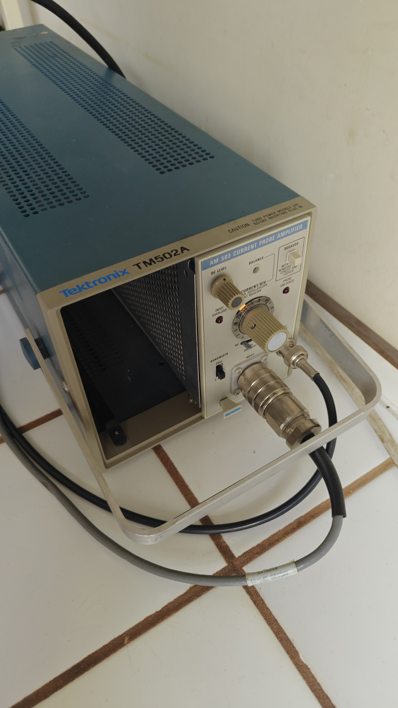
docs/Figures/Setup_Photos/current_amplifier_probe.jpg
