Teille98/HVGene-OpenHardware/docs/Figures/Setup_Photos/current_amplifier_probe_2.jpg

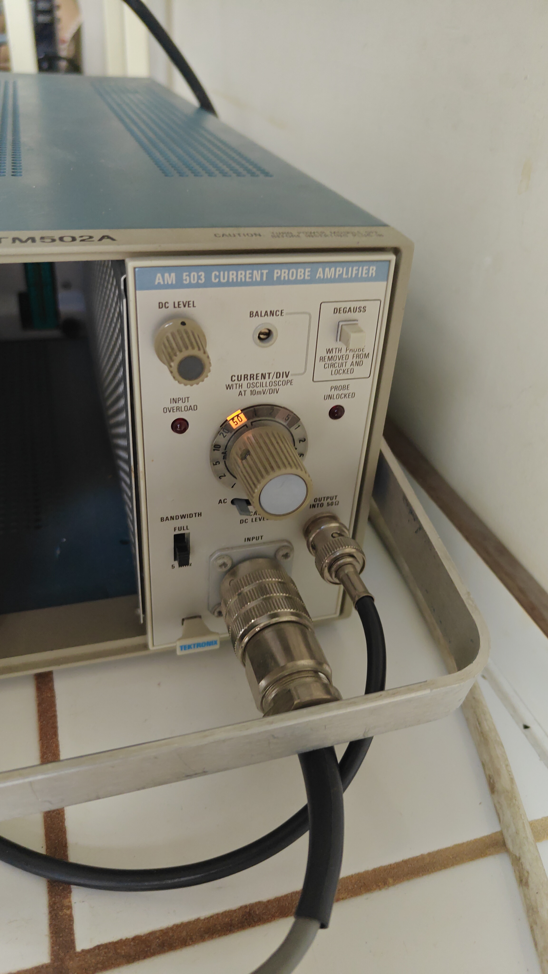
docs/Figures/Setup_Photos/current_amplifier_probe_2.jpg
