Teille98/HVGene-OpenHardware/docs/Figures/Setup_Photos/flir_1.jpg

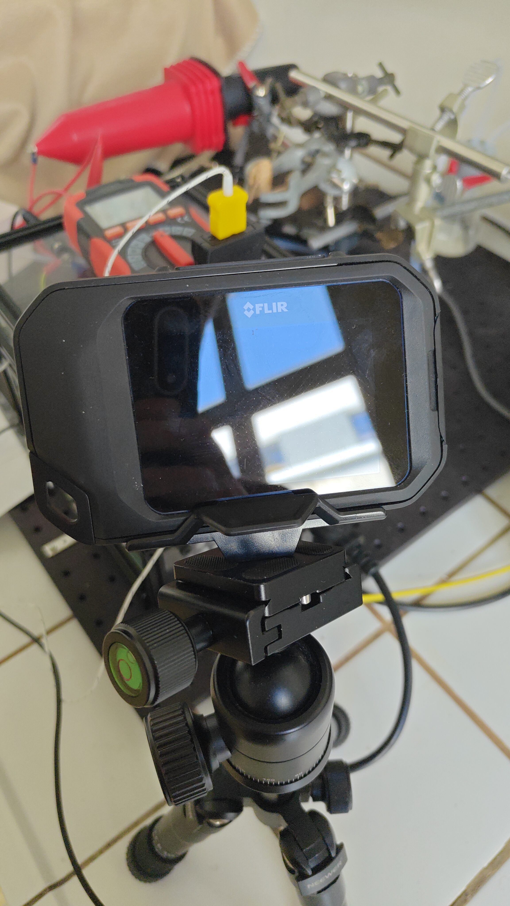
docs/Figures/Setup_Photos/flir_1.jpg
