Teille98/HVGene-OpenHardware/docs/Figures/Setup_Photos/flir_2.jpg

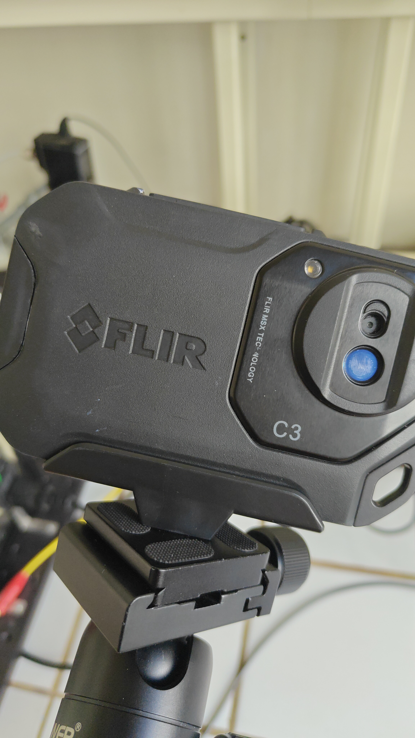
docs/Figures/Setup_Photos/flir_2.jpg
