Teille98/HVGene-OpenHardware/docs/Figures/Setup_Photos/gas_tank.jpg

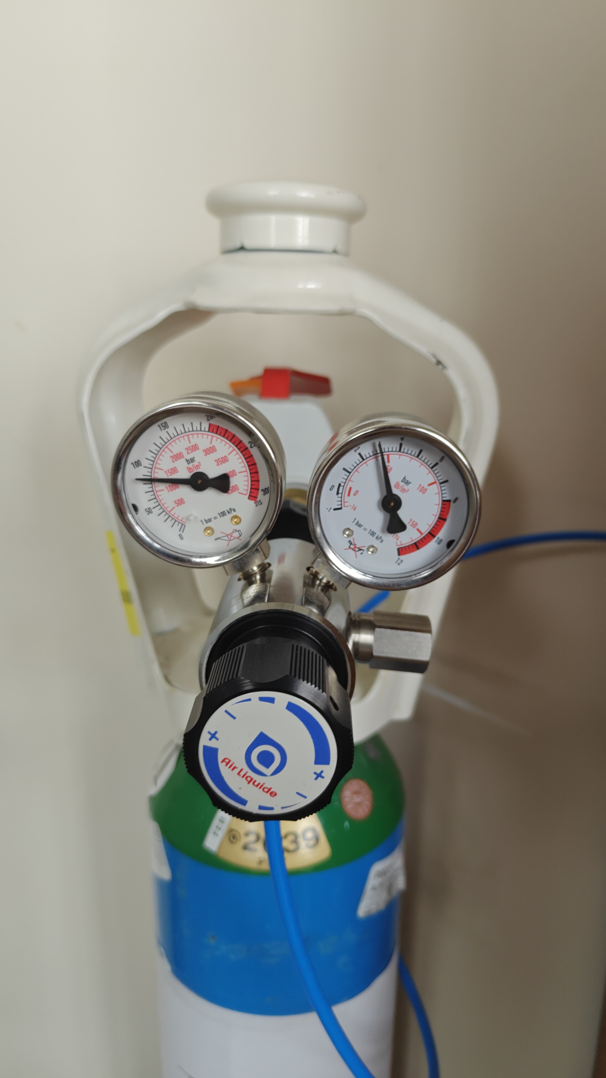
docs/Figures/Setup_Photos/gas_tank.jpg
