Teille98/HVGene-OpenHardware/docs/Figures/Setup_Photos/gasflow_controller.jpg

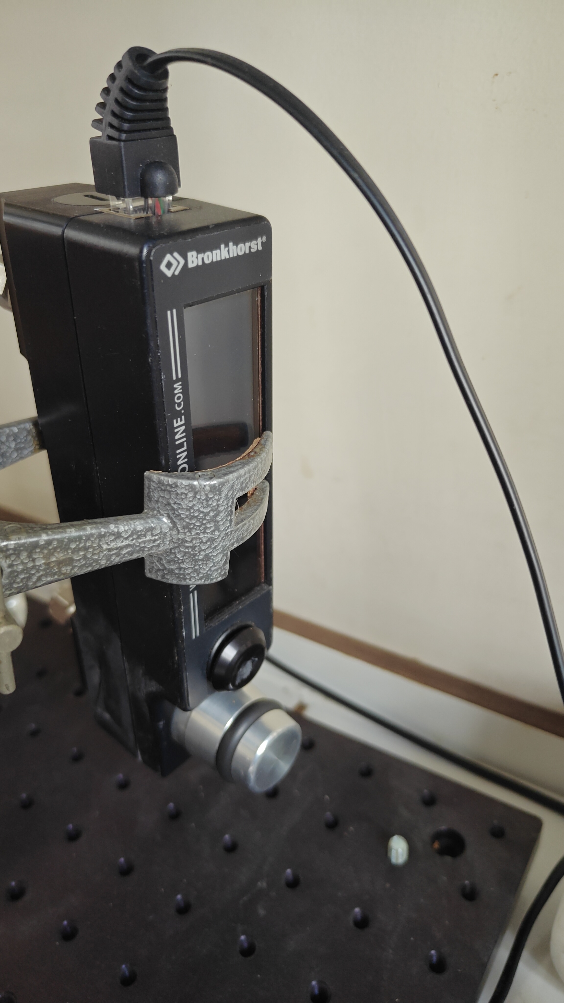
docs/Figures/Setup_Photos/gasflow_controller.jpg
