Teille98/HVGene-OpenHardware/docs/Figures/Setup_Photos/lv_probe.jpg

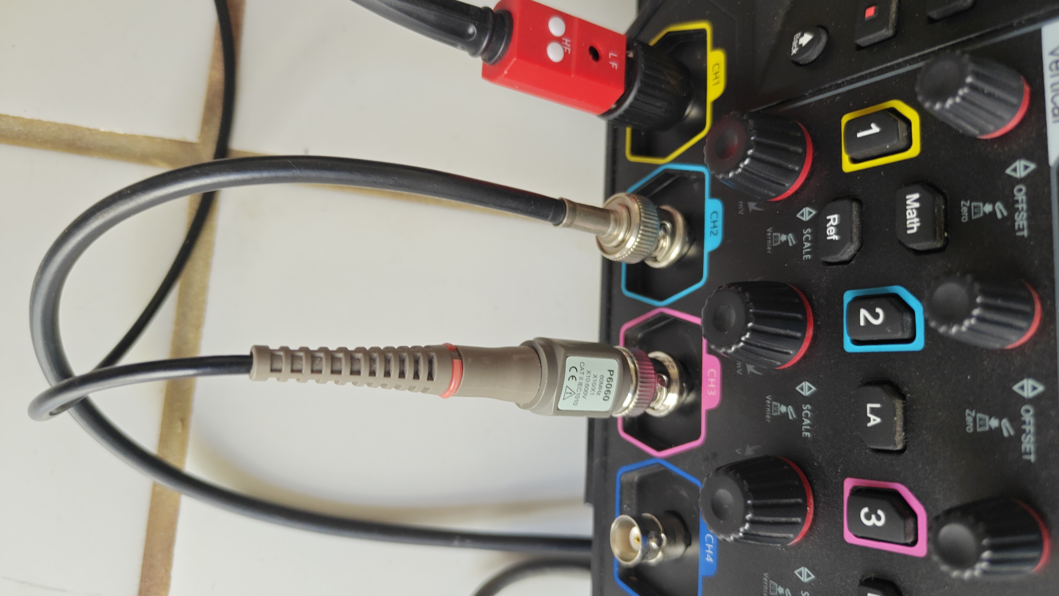
docs/Figures/Setup_Photos/lv_probe.jpg
