Teille98/HVGene-OpenHardware/docs/Figures/Setup_Photos/multimeter.jpg

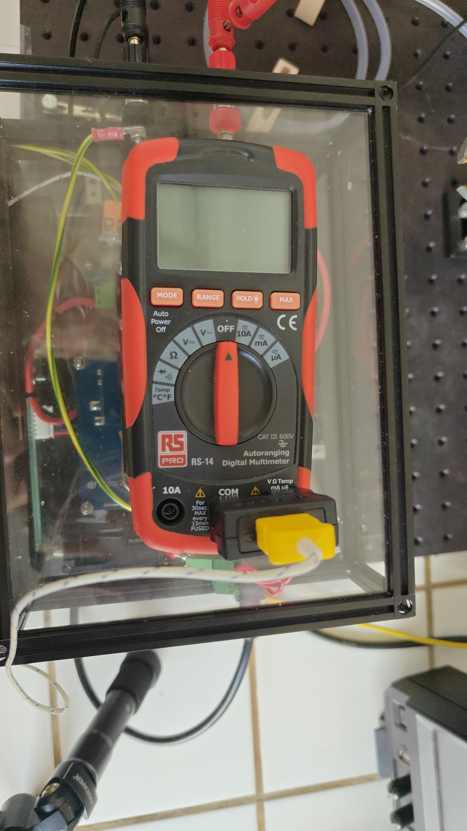
docs/Figures/Setup_Photos/multimeter.jpg
