Teille98/HVGene-OpenHardware/docs/Figures/Setup_Photos/plasma_window.jpg

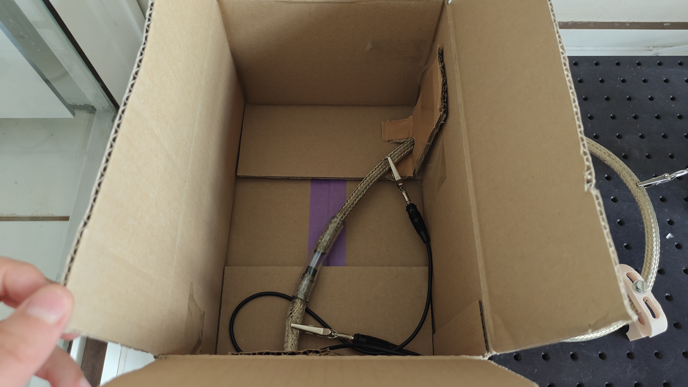
docs/Figures/Setup_Photos/plasma_window.jpg
