Teille98/HVGene-OpenHardware/docs/Figures/Setup_Photos/setup_2.jpg

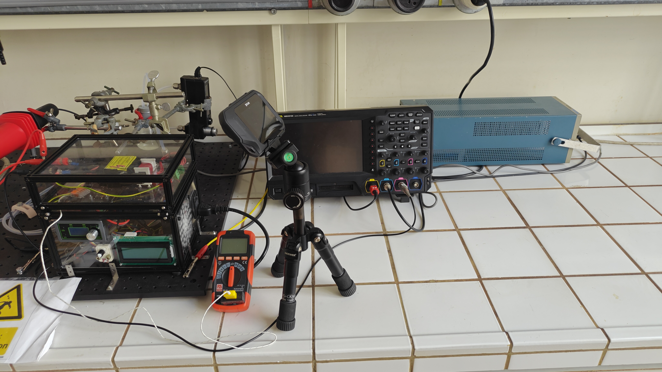
docs/Figures/Setup_Photos/setup_2.jpg
