Teille98/HVGene-OpenHardware/docs/Figures/Setup_Photos/setup_3.jpg

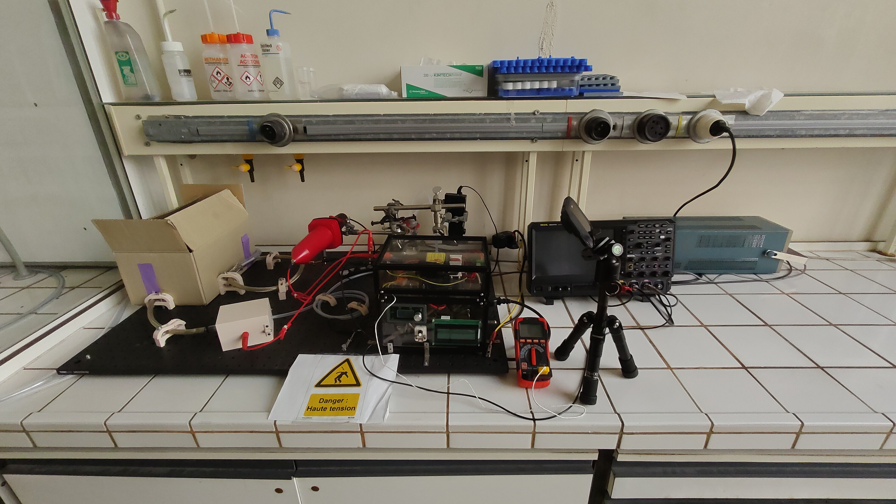
docs/Figures/Setup_Photos/setup_3.jpg
