Teille98/HVGene-OpenHardware/docs/Figures/Setup_Photos/setup_4.jpg

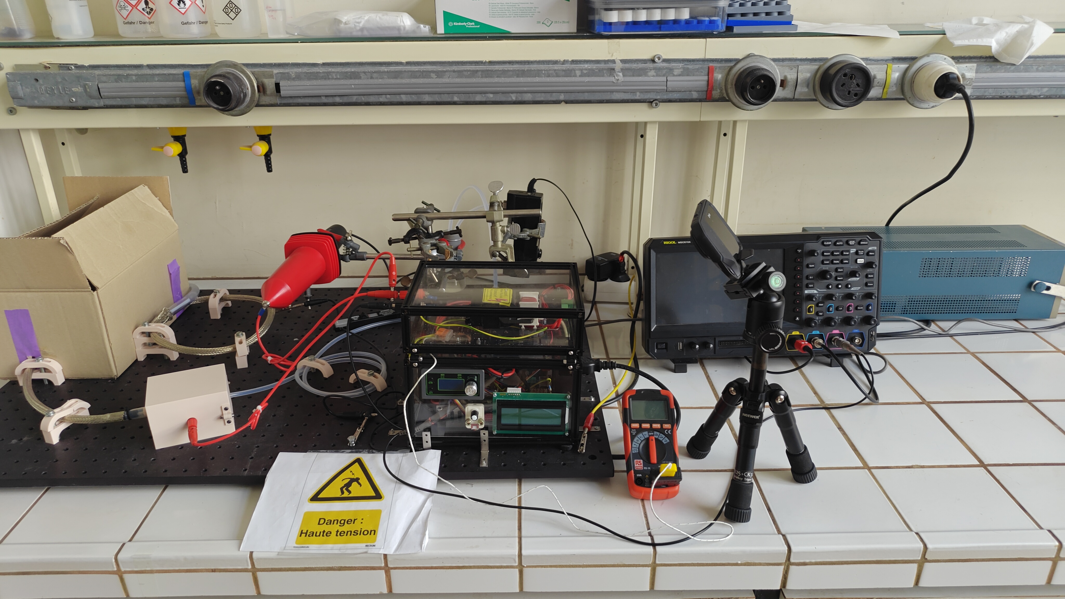
docs/Figures/Setup_Photos/setup_4.jpg
