Teille98/HVGene-OpenHardware/docs/Figures/Setup_Photos/setup_5.jpg

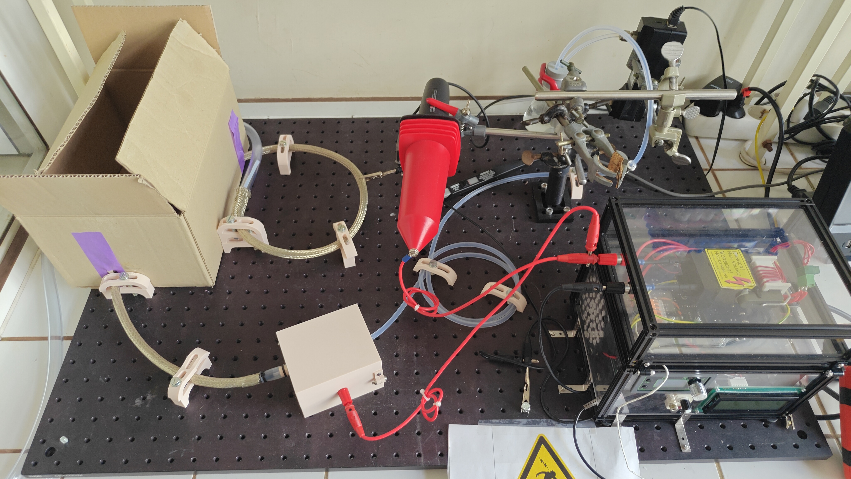
docs/Figures/Setup_Photos/setup_5.jpg
