Teille98/HVGene-OpenHardware/docs/Figures/Setup_Photos/setup_6.jpg

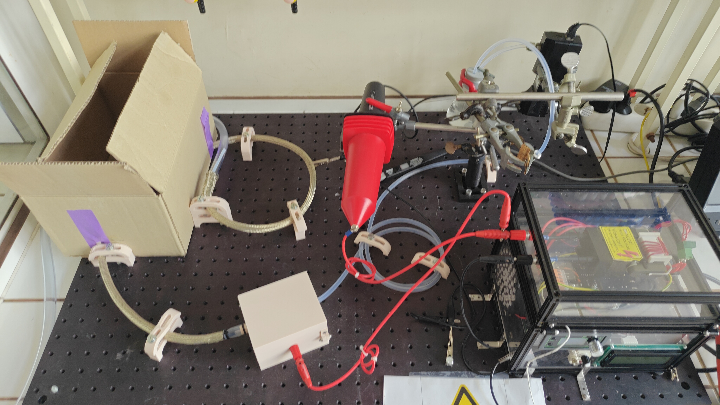
docs/Figures/Setup_Photos/setup_6.jpg
