Teille98/HVGene-OpenHardware/docs/Figures/Setup_Photos/temp_probe_Ktype.jpg

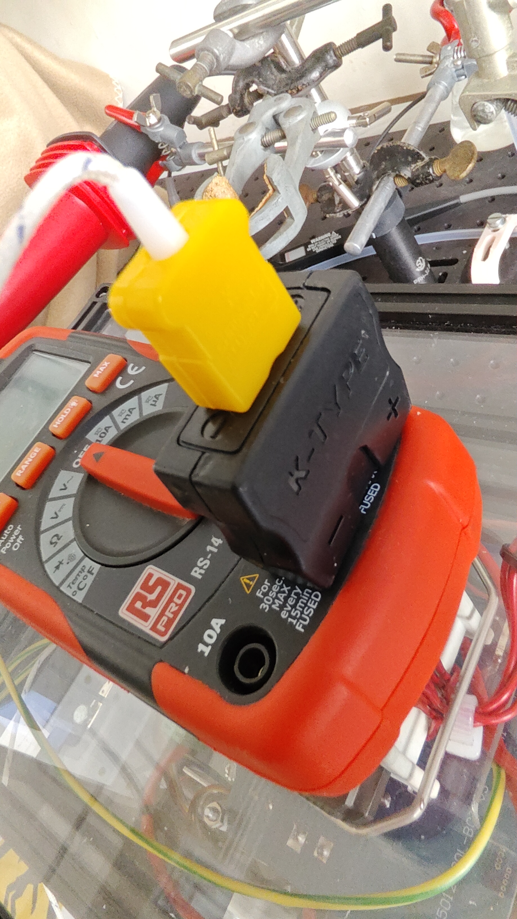
docs/Figures/Setup_Photos/temp_probe_Ktype.jpg
