Teille98/HVGene-OpenHardware/docs/Figures/Article_Figures/Fig_Val_RLCValidation.png

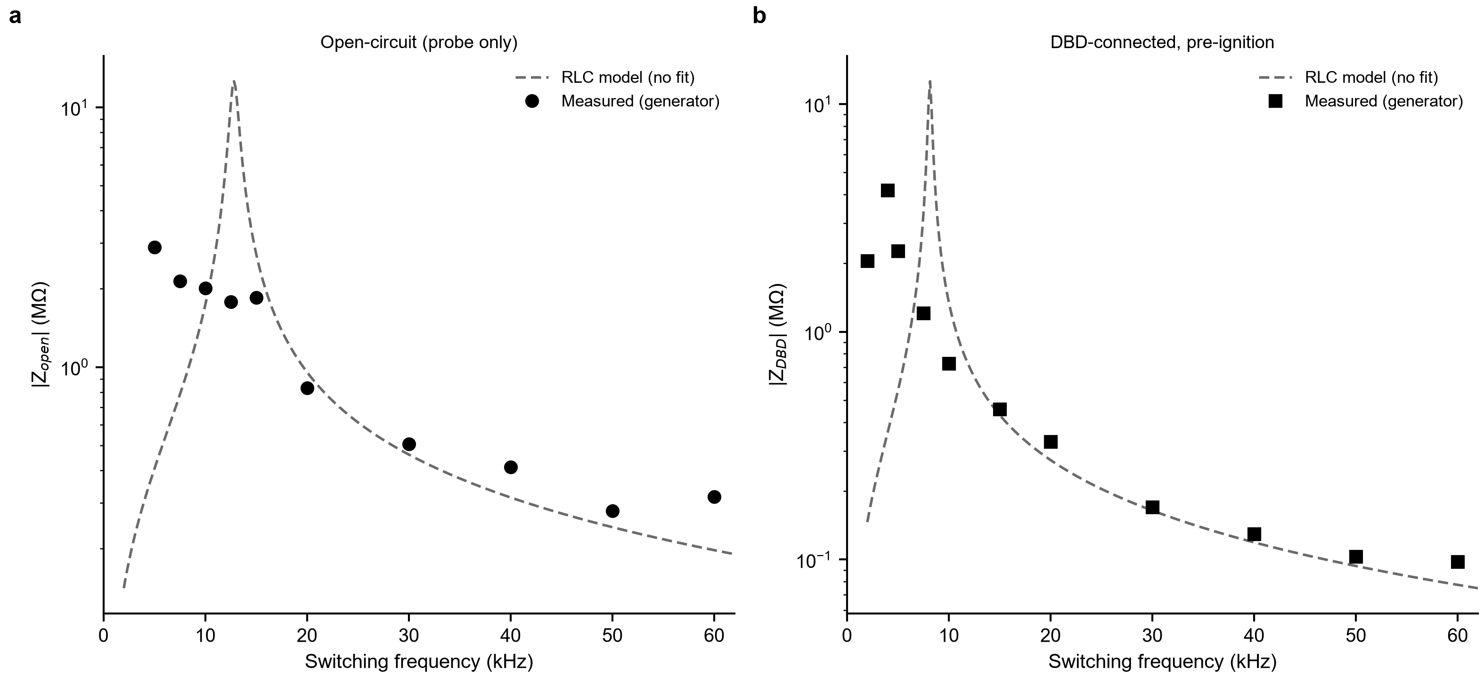
docs/Figures/Article_Figures/Fig_Val_RLCValidation.png
